Arnesh-sharma/P4P_Project-130/Testing Data/For Report/FETs/FET_CH1_Bodes/WFM02.CSV

in Sa | Frequency in Hz | Gain in dB | Phase in ° | Amplitude in Vpp
1.00E+00 | 1.000E+01 | -6.047E+01 | 1.642E+02 | 2.500E+00
2.00E+00 | 1.047E+01 | -6.065E+01 | 1.676E+02 | 2.500E+00
3.00E+00 | 1.096E+01 | -5.911E+01 | 1.651E+02 | 2.500E+00
4.00E+00 | 1.148E+01 | -5.924E+01 | 1.657E+02 | 2.500E+00
5.00E+00 | 1.202E+01 | -5.991E+01 | 1.629E+02 | 2.500E+00
6.00E+00 | 1.259E+01 | -6.114E+01 | 1.509E+02 | 2.500E+00
7.00E+00 | 1.318E+01 | -6.121E+01 | 1.619E+02 | 2.500E+00
8.00E+00 | 1.380E+01 | -6.082E+01 | 1.474E+02 | 2.500E+00
9.00E+00 | 1.445E+01 | -5.925E+01 | 1.609E+02 | 2.500E+00
1.00E+01 | 1.514E+01 | -6.002E+01 | 1.505E+02 | 2.500E+00
1.10E+01 | 1.585E+01 | -6.094E+01 | 1.486E+02 | 2.500E+00
1.20E+01 | 1.660E+01 | -5.973E+01 | 1.522E+02 | 2.500E+00
1.30E+01 | 1.738E+01 | -5.926E+01 | 1.521E+02 | 2.500E+00
1.40E+01 | 1.820E+01 | -5.986E+01 | 1.493E+02 | 2.500E+00
1.50E+01 | 1.905E+01 | -6.031E+01 | 1.430E+02 | 2.500E+00
1.60E+01 | 1.995E+01 | -6.091E+01 | 1.400E+02 | 2.500E+00
1.70E+01 | 2.089E+01 | -5.957E+01 | 1.442E+02 | 2.500E+00
1.80E+01 | 2.188E+01 | -5.907E+01 | 1.436E+02 | 2.500E+00
1.90E+01 | 2.291E+01 | -5.991E+01 | 1.474E+02 | 2.500E+00
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
