Arnesh-sharma/P4P_Project-130/Testing Data/For Report/FETs/FET_CH2_Bodes/WFM04.CSV

in Sa | Frequency in Hz | Gain in dB | Phase in ° | Amplitude in Vpp
1.00E+00 | 1.000E+01 | -6.008E+01 | 1.688E+02 | 2.500E+00
2.00E+00 | 1.047E+01 | -6.032E+01 | 1.612E+02 | 2.500E+00
3.00E+00 | 1.096E+01 | -5.910E+01 | 1.686E+02 | 2.500E+00
4.00E+00 | 1.148E+01 | -6.008E+01 | 1.629E+02 | 2.500E+00
5.00E+00 | 1.202E+01 | -5.858E+01 | 1.622E+02 | 2.500E+00
6.00E+00 | 1.259E+01 | -5.917E+01 | 1.635E+02 | 2.500E+00
7.00E+00 | 1.318E+01 | -5.980E+01 | 1.564E+02 | 2.500E+00
8.00E+00 | 1.380E+01 | -5.957E+01 | 1.568E+02 | 2.500E+00
9.00E+00 | 1.445E+01 | -6.005E+01 | 1.624E+02 | 2.500E+00
1.00E+01 | 1.514E+01 | -6.035E+01 | 1.547E+02 | 2.500E+00
1.10E+01 | 1.585E+01 | -5.988E+01 | 1.471E+02 | 2.500E+00
1.20E+01 | 1.660E+01 | -6.016E+01 | 1.517E+02 | 2.500E+00
1.30E+01 | 1.738E+01 | -5.981E+01 | 1.529E+02 | 2.500E+00
1.40E+01 | 1.820E+01 | -5.945E+01 | 1.495E+02 | 2.500E+00
1.50E+01 | 1.905E+01 | -6.048E+01 | 1.459E+02 | 2.500E+00
1.60E+01 | 1.995E+01 | -6.108E+01 | 1.517E+02 | 2.500E+00
1.70E+01 | 2.089E+01 | -5.919E+01 | 1.538E+02 | 2.500E+00
1.80E+01 | 2.188E+01 | -6.028E+01 | 1.495E+02 | 2.500E+00
1.90E+01 | 2.291E+01 | -5.945E+01 | 1.537E+02 | 2.500E+00
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
