Arnesh-sharma/P4P_Project-130/Testing Data/For Report/FETs/FET_PCB_CH1_Bodes/WFM05.CSV

in Sa | Frequency in Hz | Gain in dB | Phase in ° | Amplitude in Vpp
1.00E+00 | 1.000E+01 | -3.042E+01 | -7.533E+01 | 2.500E+00
2.00E+00 | 1.047E+01 | -3.042E+01 | -7.579E+01 | 2.500E+00
3.00E+00 | 1.096E+01 | -3.021E+01 | -7.619E+01 | 2.500E+00
4.00E+00 | 1.148E+01 | -3.033E+01 | -7.878E+01 | 2.500E+00
5.00E+00 | 1.202E+01 | -3.009E+01 | -7.882E+01 | 2.500E+00
6.00E+00 | 1.259E+01 | -3.027E+01 | -8.114E+01 | 2.500E+00
7.00E+00 | 1.318E+01 | -3.026E+01 | -8.289E+01 | 2.500E+00
8.00E+00 | 1.380E+01 | -3.015E+01 | -8.408E+01 | 2.500E+00
9.00E+00 | 1.445E+01 | -3.002E+01 | -8.246E+01 | 2.500E+00
1.00E+01 | 1.514E+01 | -3.021E+01 | -8.605E+01 | 2.500E+00
1.10E+01 | 1.585E+01 | -3.003E+01 | -8.678E+01 | 2.500E+00
1.20E+01 | 1.660E+01 | -2.995E+01 | -8.854E+01 | 2.500E+00
1.30E+01 | 1.738E+01 | -2.990E+01 | -8.868E+01 | 2.500E+00
1.40E+01 | 1.820E+01 | -3.001E+01 | -9.140E+01 | 2.500E+00
1.50E+01 | 1.905E+01 | -3.006E+01 | -9.274E+01 | 2.500E+00
1.60E+01 | 1.995E+01 | -2.995E+01 | -9.309E+01 | 2.500E+00
1.70E+01 | 2.089E+01 | -2.965E+01 | -9.219E+01 | 2.500E+00
1.80E+01 | 2.188E+01 | -2.967E+01 | -9.439E+01 | 2.500E+00
1.90E+01 | 2.291E+01 | -2.963E+01 | -9.443E+01 | 2.500E+00
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
