Arnesh-sharma/P4P_Project-130/Testing Data/For Report/FETs/FET_PCB_CH2_Bodes/WFM07.CSV

in Sa | Frequency in Hz | Gain in dB | Phase in ° | Amplitude in Vpp
1.00E+00 | 1.000E+01 | -6.133E+01 | 1.636E+02 | 2.500E+00
2.00E+00 | 1.047E+01 | -6.054E+01 | 1.682E+02 | 2.500E+00
3.00E+00 | 1.096E+01 | -6.137E+01 | 1.630E+02 | 2.500E+00
4.00E+00 | 1.148E+01 | -6.084E+01 | 1.671E+02 | 2.500E+00
5.00E+00 | 1.202E+01 | -5.939E+01 | 1.590E+02 | 2.500E+00
6.00E+00 | 1.259E+01 | -6.143E+01 | 1.571E+02 | 2.500E+00
7.00E+00 | 1.318E+01 | -6.131E+01 | 1.496E+02 | 2.500E+00
8.00E+00 | 1.380E+01 | -6.033E+01 | 1.673E+02 | 2.500E+00
9.00E+00 | 1.445E+01 | -5.975E+01 | 1.576E+02 | 2.500E+00
1.00E+01 | 1.514E+01 | -6.128E+01 | 1.471E+02 | 2.500E+00
1.10E+01 | 1.585E+01 | -6.025E+01 | 1.496E+02 | 2.500E+00
1.20E+01 | 1.660E+01 | -6.090E+01 | 1.441E+02 | 2.500E+00
1.30E+01 | 1.738E+01 | -6.105E+01 | 1.563E+02 | 2.500E+00
1.40E+01 | 1.820E+01 | -6.109E+01 | 1.546E+02 | 2.500E+00
1.50E+01 | 1.905E+01 | -6.118E+01 | 1.469E+02 | 2.500E+00
1.60E+01 | 1.995E+01 | -6.015E+01 | 1.507E+02 | 2.500E+00
1.70E+01 | 2.089E+01 | -6.005E+01 | 1.497E+02 | 2.500E+00
1.80E+01 | 2.188E+01 | -6.015E+01 | 1.510E+02 | 2.500E+00
1.90E+01 | 2.291E+01 | -5.955E+01 | 1.421E+02 | 2.500E+00
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
