Arnesh-sharma/P4P_Project-130/Testing Data/For Report/FETs/self-biasing/WFM06.CSV

in Sa | Frequency in Hz | Gain in dB | Phase in ° | Amplitude in Vpp
1.00E+00 | 1.000E+01 | -6.061E+01 | 1.585E+02 | 2.500E+00
2.00E+00 | 1.047E+01 | -6.017E+01 | 1.648E+02 | 2.500E+00
3.00E+00 | 1.096E+01 | -5.976E+01 | 1.714E+02 | 2.500E+00
4.00E+00 | 1.148E+01 | -5.970E+01 | 1.749E+02 | 2.500E+00
5.00E+00 | 1.202E+01 | -6.005E+01 | 1.654E+02 | 2.500E+00
6.00E+00 | 1.259E+01 | -6.053E+01 | 1.615E+02 | 2.500E+00
7.00E+00 | 1.318E+01 | -6.161E+01 | 1.511E+02 | 2.500E+00
8.00E+00 | 1.380E+01 | -6.113E+01 | 1.616E+02 | 2.500E+00
9.00E+00 | 1.445E+01 | -6.097E+01 | 1.599E+02 | 2.500E+00
1.00E+01 | 1.514E+01 | -6.154E+01 | 1.647E+02 | 2.500E+00
1.10E+01 | 1.585E+01 | -6.083E+01 | 1.540E+02 | 2.500E+00
1.20E+01 | 1.660E+01 | -6.118E+01 | 1.557E+02 | 2.500E+00
1.30E+01 | 1.738E+01 | -6.055E+01 | 1.540E+02 | 2.500E+00
1.40E+01 | 1.820E+01 | -6.116E+01 | 1.457E+02 | 2.500E+00
1.50E+01 | 1.905E+01 | -6.225E+01 | 1.432E+02 | 2.500E+00
1.60E+01 | 1.995E+01 | -6.075E+01 | 1.471E+02 | 2.500E+00
1.70E+01 | 2.089E+01 | -6.008E+01 | 1.429E+02 | 2.500E+00
1.80E+01 | 2.188E+01 | -5.997E+01 | 1.408E+02 | 2.500E+00
1.90E+01 | 2.291E+01 | -6.139E+01 | 1.360E+02 | 2.500E+00
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
