Arnesh-sharma/P4P_Project-130/Testing Data/For Report/FETs/self-biasing/WFM08.CSV

in Sa | Frequency in Hz | Gain in dB | Phase in ° | Amplitude in Vpp
1.00E+00 | 1.000E+01 | -6.133E+01 | 1.578E+02 | 2.500E+00
2.00E+00 | 1.047E+01 | -6.377E+01 | 1.590E+02 | 2.500E+00
3.00E+00 | 1.096E+01 | -6.002E+01 | 1.534E+02 | 2.500E+00
4.00E+00 | 1.148E+01 | -6.130E+01 | 1.545E+02 | 2.500E+00
5.00E+00 | 1.202E+01 | -6.123E+01 | 1.655E+02 | 2.500E+00
6.00E+00 | 1.259E+01 | -6.051E+01 | 1.588E+02 | 2.500E+00
7.00E+00 | 1.318E+01 | -6.065E+01 | 1.642E+02 | 2.500E+00
8.00E+00 | 1.380E+01 | -6.114E+01 | 1.550E+02 | 2.500E+00
9.00E+00 | 1.445E+01 | -5.991E+01 | 1.567E+02 | 2.500E+00
1.00E+01 | 1.514E+01 | -6.283E+01 | 1.500E+02 | 2.500E+00
1.10E+01 | 1.585E+01 | -6.063E+01 | 1.496E+02 | 2.500E+00
1.20E+01 | 1.660E+01 | -6.056E+01 | 1.499E+02 | 2.500E+00
1.30E+01 | 1.738E+01 | -5.967E+01 | 1.531E+02 | 2.500E+00
1.40E+01 | 1.820E+01 | -6.410E+01 | 1.441E+02 | 2.500E+00
1.50E+01 | 1.905E+01 | -6.209E+01 | 1.359E+02 | 2.500E+00
1.60E+01 | 1.995E+01 | -6.193E+01 | 1.447E+02 | 2.500E+00
1.70E+01 | 2.089E+01 | -5.917E+01 | 1.486E+02 | 2.500E+00
1.80E+01 | 2.188E+01 | -6.021E+01 | 1.463E+02 | 2.500E+00
1.90E+01 | 2.291E+01 | -6.020E+01 | 1.390E+02 | 2.500E+00
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
