Arnesh-sharma/P4P_Project-130/Testing Data/For Report/Instrumentation Amp Circuit/Capacitors Shorted/WFM08.CSV

in Sa | Frequency in Hz | Gain in dB | Phase in ° | Amplitude in Vpp
1.00E+00 | 1.000E+01 | -5.101E+01 | 9.313E+01 | 2.500E+00
2.00E+00 | 1.047E+01 | -5.222E+01 | 7.926E+01 | 2.500E+00
3.00E+00 | 1.096E+01 | -5.104E+01 | 8.657E+01 | 2.500E+00
4.00E+00 | 1.148E+01 | -4.765E+01 | 7.619E+01 | 2.500E+00
5.00E+00 | 1.202E+01 | -4.724E+01 | 1.038E+02 | 2.500E+00
6.00E+00 | 1.259E+01 | -4.641E+01 | 9.072E+01 | 2.500E+00
7.00E+00 | 1.318E+01 | -4.665E+01 | 9.873E+01 | 2.500E+00
8.00E+00 | 1.380E+01 | -4.859E+01 | 8.802E+01 | 2.500E+00
9.00E+00 | 1.445E+01 | -5.057E+01 | 9.474E+01 | 2.500E+00
1.00E+01 | 1.514E+01 | -4.840E+01 | 8.466E+01 | 2.500E+00
1.10E+01 | 1.585E+01 | -4.513E+01 | 7.512E+01 | 2.500E+00
1.20E+01 | 1.660E+01 | -4.788E+01 | 8.815E+01 | 2.500E+00
1.30E+01 | 1.738E+01 | -4.551E+01 | 7.494E+01 | 2.500E+00
1.40E+01 | 1.820E+01 | -4.634E+01 | 9.491E+01 | 2.500E+00
1.50E+01 | 1.905E+01 | -4.476E+01 | 7.654E+01 | 2.500E+00
1.60E+01 | 1.995E+01 | -4.693E+01 | 7.954E+01 | 2.500E+00
1.70E+01 | 2.089E+01 | -4.634E+01 | 9.863E+01 | 2.500E+00
1.80E+01 | 2.188E+01 | -4.537E+01 | 8.156E+01 | 2.500E+00
1.90E+01 | 2.291E+01 | -4.388E+01 | 9.160E+01 | 2.500E+00
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
