Arnesh-sharma/P4P_Project-130/Testing Data/For Report/archieved/Larger_distance/WFM02.CSV

in Sa | Frequency in Hz | Gain in dB | Phase in ° | Amplitude in Vpp
1.00E+00 | 1.000E+01 | -5.203E+01 | 1.149E+02 | 2.500E+00
2.00E+00 | 1.047E+01 | -5.043E+01 | 1.090E+02 | 2.500E+00
3.00E+00 | 1.096E+01 | -5.006E+01 | 1.136E+02 | 2.500E+00
4.00E+00 | 1.148E+01 | -4.958E+01 | 1.174E+02 | 2.500E+00
5.00E+00 | 1.202E+01 | -4.828E+01 | 1.049E+02 | 2.500E+00
6.00E+00 | 1.259E+01 | -4.667E+01 | 1.065E+02 | 2.500E+00
7.00E+00 | 1.318E+01 | -4.695E+01 | 8.723E+01 | 2.500E+00
8.00E+00 | 1.380E+01 | -4.717E+01 | 1.143E+02 | 2.500E+00
9.00E+00 | 1.445E+01 | -4.784E+01 | 1.038E+02 | 2.500E+00
1.00E+01 | 1.514E+01 | -4.713E+01 | 1.044E+02 | 2.500E+00
1.10E+01 | 1.585E+01 | -4.480E+01 | 1.026E+02 | 2.500E+00
1.20E+01 | 1.660E+01 | -4.749E+01 | 1.006E+02 | 2.500E+00
1.30E+01 | 1.738E+01 | -4.628E+01 | 1.056E+02 | 2.500E+00
1.40E+01 | 1.820E+01 | -4.692E+01 | 9.501E+01 | 2.500E+00
1.50E+01 | 1.905E+01 | -4.497E+01 | 1.049E+02 | 2.500E+00
1.60E+01 | 1.995E+01 | -4.505E+01 | 8.538E+01 | 2.500E+00
1.70E+01 | 2.089E+01 | -4.315E+01 | 8.804E+01 | 2.500E+00
1.80E+01 | 2.188E+01 | -4.538E+01 | 8.958E+01 | 2.500E+00
1.90E+01 | 2.291E+01 | -4.209E+01 | 9.914E+01 | 2.500E+00
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
