Arnesh-sharma/P4P_Project-130/Testing Data/For Report/FETs/single_stage/WFM01.CSV

in Sa | Frequency in Hz | Gain in dB | Phase in ° | Amplitude in Vpp
1.00E+00 | 1.000E+01 | -5.988E+01 | 1.644E+02 | 2.500E+00
2.00E+00 | 1.047E+01 | -6.120E+01 | 1.702E+02 | 2.500E+00
3.00E+00 | 1.096E+01 | -5.895E+01 | 1.637E+02 | 2.500E+00
4.00E+00 | 1.148E+01 | -5.893E+01 | 1.624E+02 | 2.500E+00
5.00E+00 | 1.202E+01 | -5.933E+01 | 1.627E+02 | 2.500E+00
6.00E+00 | 1.259E+01 | -5.953E+01 | 1.594E+02 | 2.500E+00
7.00E+00 | 1.318E+01 | -6.090E+01 | 1.557E+02 | 2.500E+00
8.00E+00 | 1.380E+01 | -6.072E+01 | 1.570E+02 | 2.500E+00
9.00E+00 | 1.445E+01 | -5.999E+01 | 1.594E+02 | 2.500E+00
1.00E+01 | 1.514E+01 | -6.031E+01 | 1.593E+02 | 2.500E+00
1.10E+01 | 1.585E+01 | -6.077E+01 | 1.564E+02 | 2.500E+00
1.20E+01 | 1.660E+01 | -6.075E+01 | 1.445E+02 | 2.500E+00
1.30E+01 | 1.738E+01 | -6.028E+01 | 1.560E+02 | 2.500E+00
1.40E+01 | 1.820E+01 | -6.079E+01 | 1.498E+02 | 2.500E+00
1.50E+01 | 1.905E+01 | -6.085E+01 | 1.419E+02 | 2.500E+00
1.60E+01 | 1.995E+01 | -5.956E+01 | 1.446E+02 | 2.500E+00
1.70E+01 | 2.089E+01 | -5.898E+01 | 1.546E+02 | 2.500E+00
1.80E+01 | 2.188E+01 | -5.962E+01 | 1.493E+02 | 2.500E+00
1.90E+01 | 2.291E+01 | -5.903E+01 | 1.380E+02 | 2.500E+00
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
