Arnesh-sharma/P4P_Project-130/Testing Data/For Report/FETs/single_stage/WFM03.CSV

in Sa | Frequency in Hz | Gain in dB | Phase in ° | Amplitude in Vpp
1.00E+00 | 1.000E+01 | -5.998E+01 | 1.650E+02 | 2.500E+00
2.00E+00 | 1.047E+01 | -6.008E+01 | 1.716E+02 | 2.500E+00
3.00E+00 | 1.096E+01 | -5.981E+01 | 1.618E+02 | 2.500E+00
4.00E+00 | 1.148E+01 | -6.136E+01 | 1.599E+02 | 2.500E+00
5.00E+00 | 1.202E+01 | -6.048E+01 | 1.658E+02 | 2.500E+00
6.00E+00 | 1.259E+01 | -6.148E+01 | 1.579E+02 | 2.500E+00
7.00E+00 | 1.318E+01 | -5.994E+01 | 1.582E+02 | 2.500E+00
8.00E+00 | 1.380E+01 | -5.983E+01 | 1.653E+02 | 2.500E+00
9.00E+00 | 1.445E+01 | -5.953E+01 | 1.660E+02 | 2.500E+00
1.00E+01 | 1.514E+01 | -6.018E+01 | 1.623E+02 | 2.500E+00
1.10E+01 | 1.585E+01 | -6.015E+01 | 1.556E+02 | 2.500E+00
1.20E+01 | 1.660E+01 | -5.983E+01 | 1.547E+02 | 2.500E+00
1.30E+01 | 1.738E+01 | -5.961E+01 | 1.544E+02 | 2.500E+00
1.40E+01 | 1.820E+01 | -6.047E+01 | 1.511E+02 | 2.500E+00
1.50E+01 | 1.905E+01 | -6.066E+01 | 1.537E+02 | 2.500E+00
1.60E+01 | 1.995E+01 | -6.006E+01 | 1.462E+02 | 2.500E+00
1.70E+01 | 2.089E+01 | -5.886E+01 | 1.445E+02 | 2.500E+00
1.80E+01 | 2.188E+01 | -5.851E+01 | 1.504E+02 | 2.500E+00
1.90E+01 | 2.291E+01 | -6.026E+01 | 1.458E+02 | 2.500E+00
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
