Arnesh-sharma/P4P_Project-130/Matlab Code/Electret_sensor/300Hz_electret.png

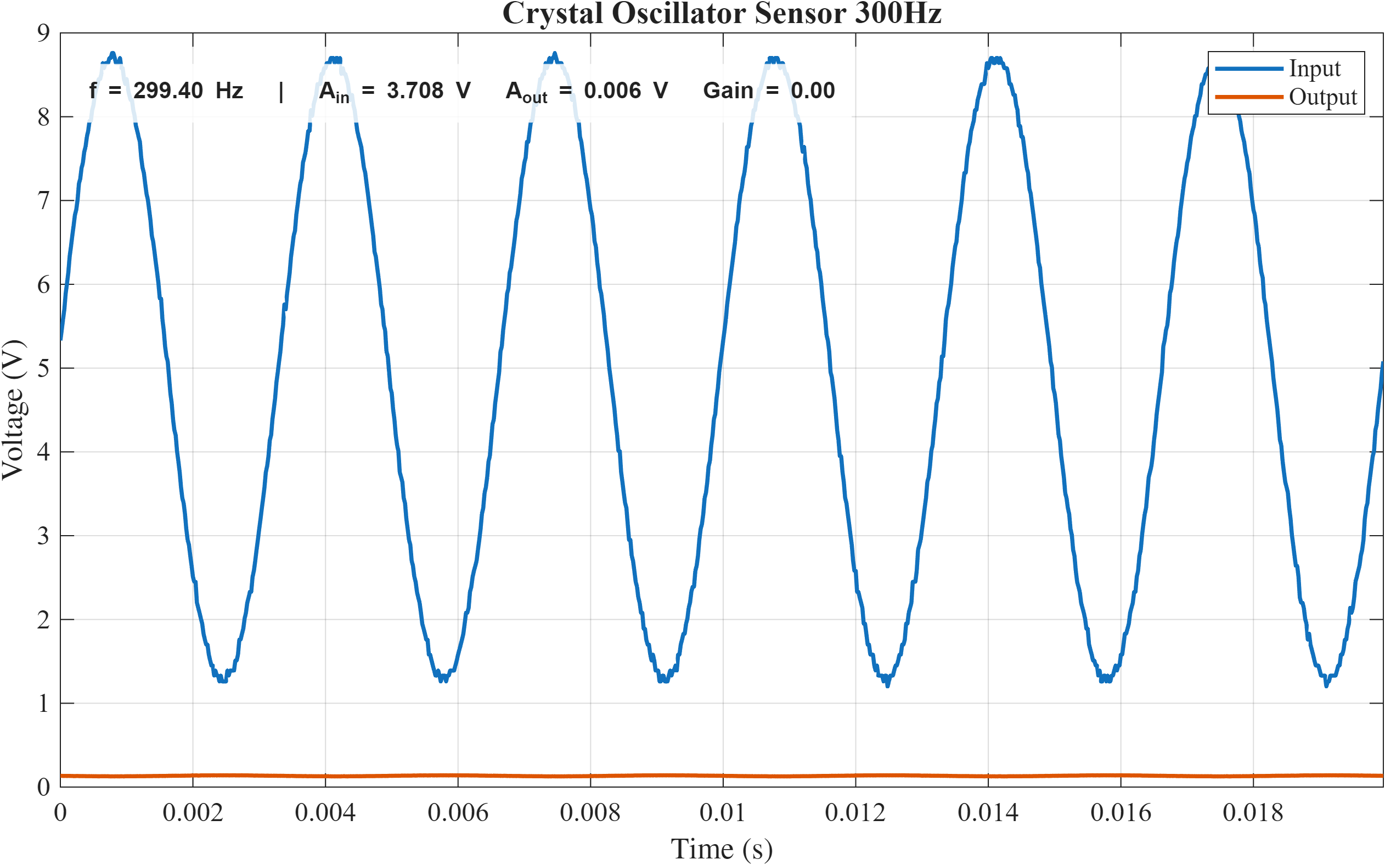
Matlab Code/Electret_sensor/300Hz_electret.png
