Arnesh-sharma/P4P_Project-130/Matlab Code/Electret_sensor/electret_plot.png

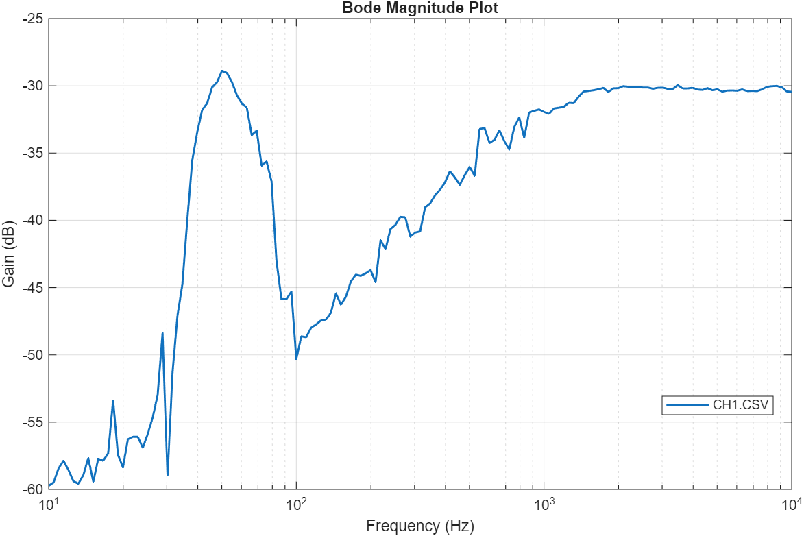
Matlab Code/Electret_sensor/electret_plot.png
