Arnesh-sharma/P4P_Project-130/Matlab Code/electret_single_labelled.png

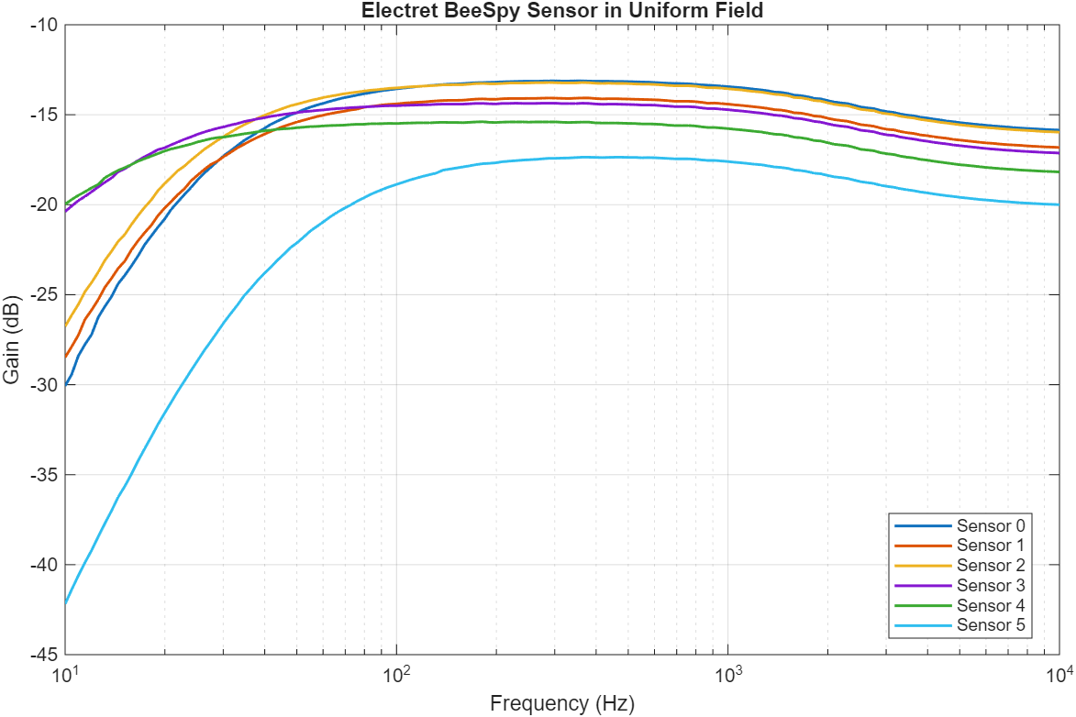
Matlab Code/electret_single_labelled.png
