Arnesh-sharma/P4P_Project-130/Matlab Code/IA_Sensor_Data/combined_bode_(inc short channel).png

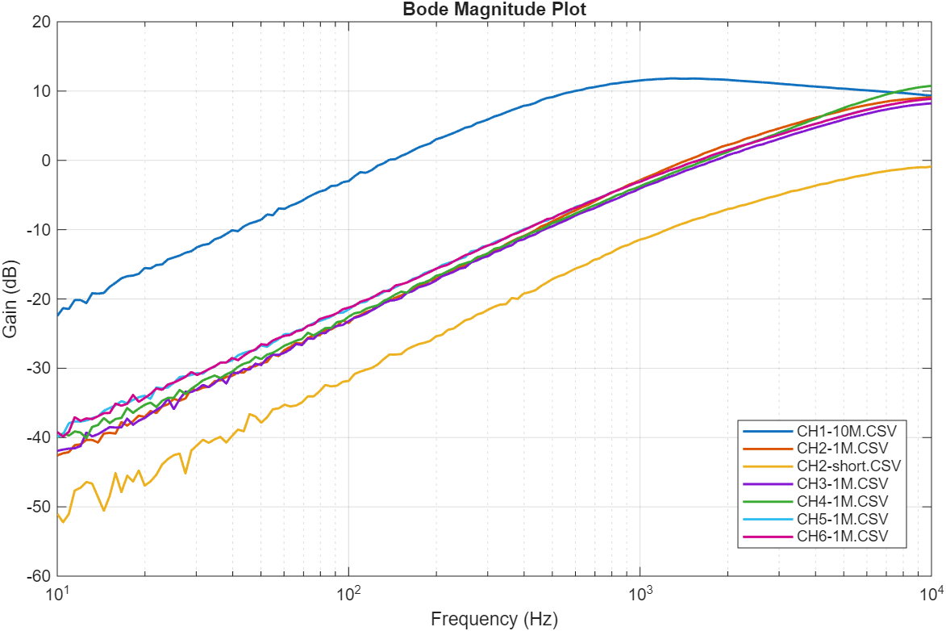
Matlab Code/IA_Sensor_Data/combined_bode_(inc short channel).png
