Arnesh-sharma/P4P_Project-130/Matlab Code/IA_Sensor_Data/instrumentation_amp_plot.png

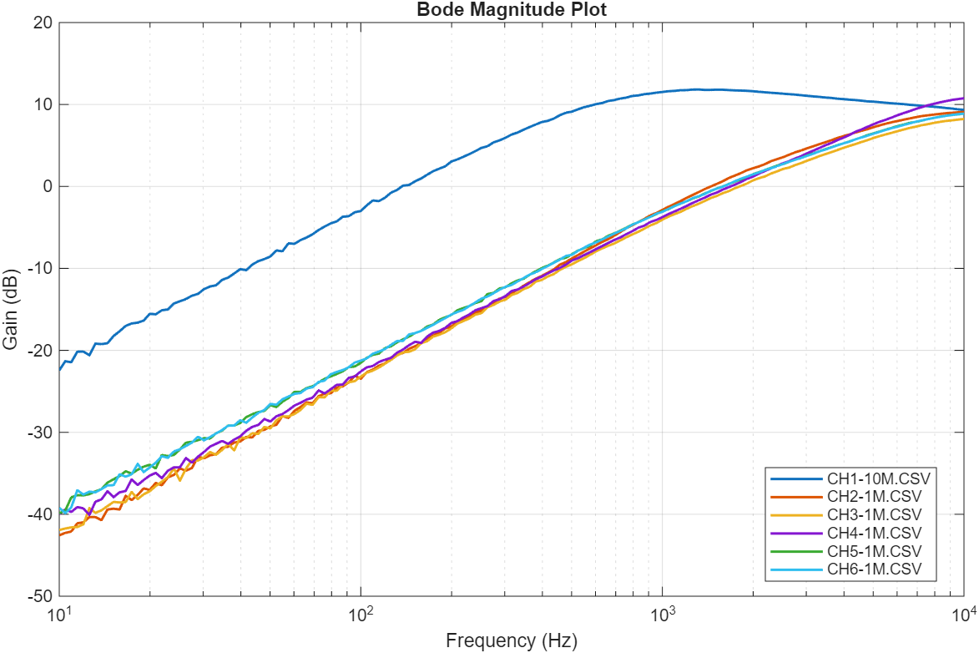
Matlab Code/IA_Sensor_Data/instrumentation_amp_plot.png
