Arnesh-sharma/P4P_Project-130/Matlab Code/jfet_plate_labelled.png

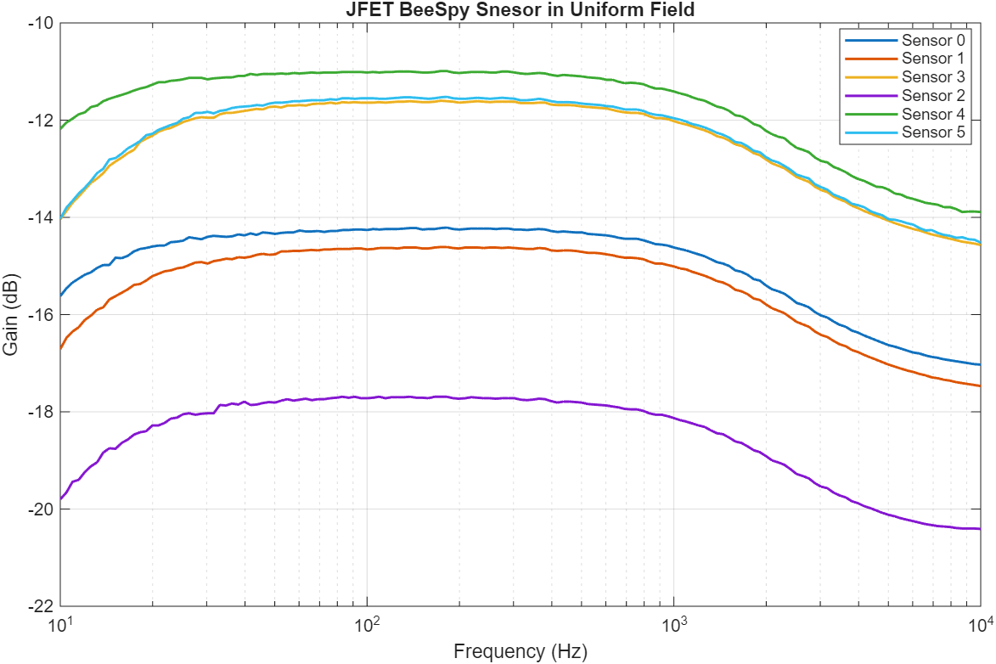
Matlab Code/jfet_plate_labelled.png
