Arnesh-sharma/P4P_Project-130/Matlab Code/jfet_vero_self_biasing.png

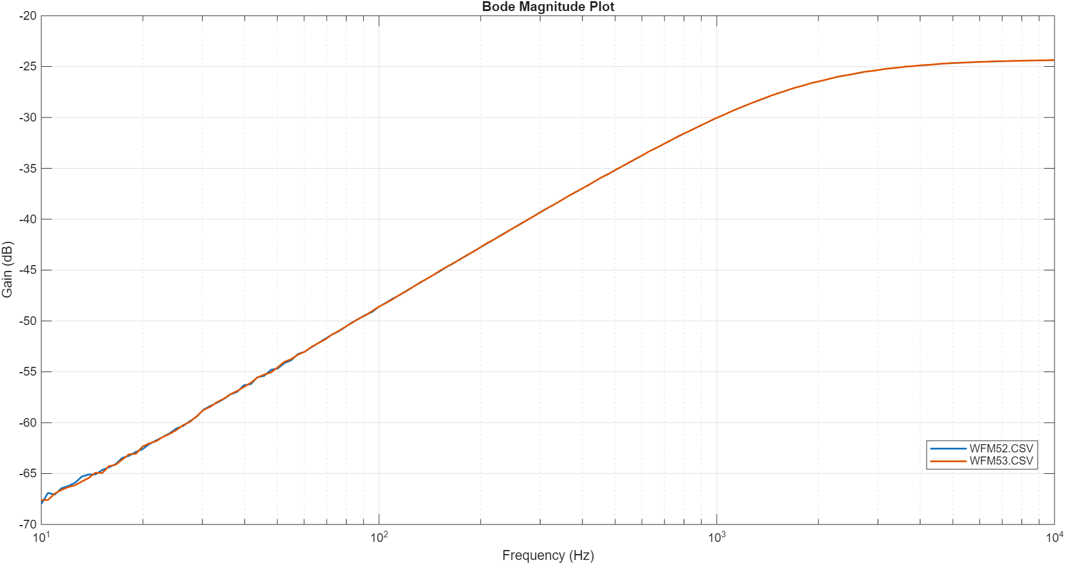
Matlab Code/jfet_vero_self_biasing.png
