Arnesh-sharma/P4P_Project-130/Matlab Code/jfet_vero_single_stage_CH2.png

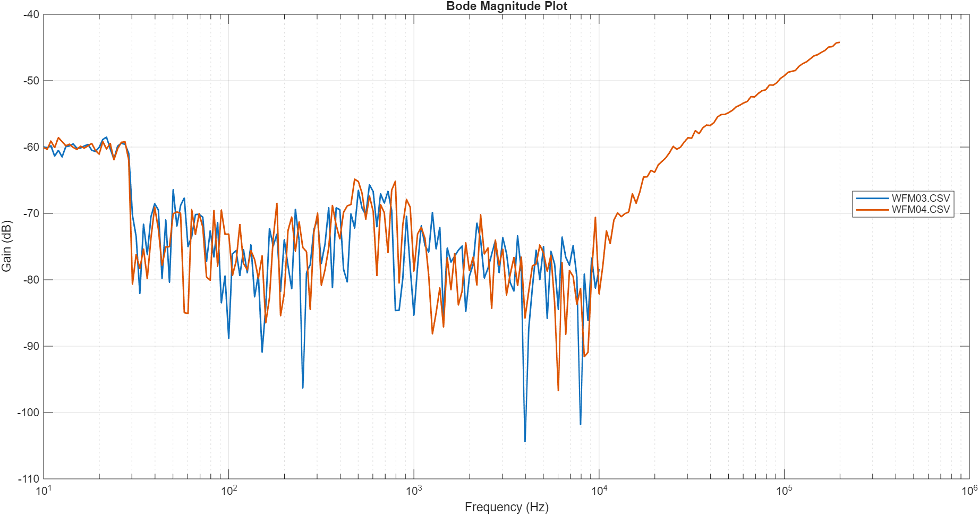
Matlab Code/jfet_vero_single_stage_CH2.png
