Arnesh-sharma/P4P_Project-130/Photos/10Meg Resistor Chain.jpg

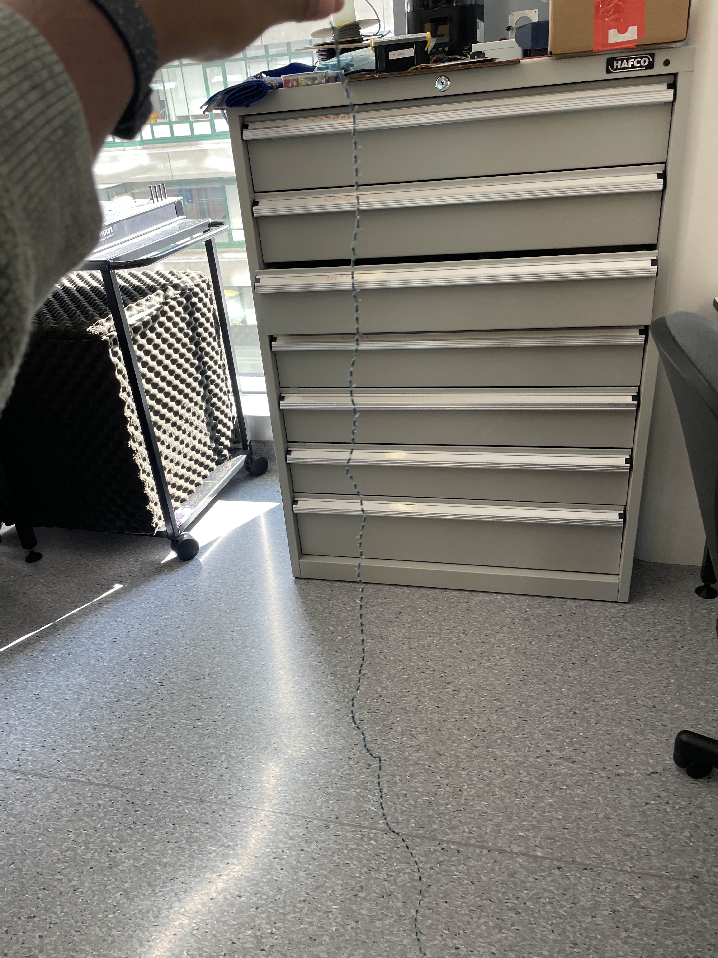
Photos/10Meg Resistor Chain.jpg
