Arnesh-sharma/P4P_Project-130/Photos/image.png

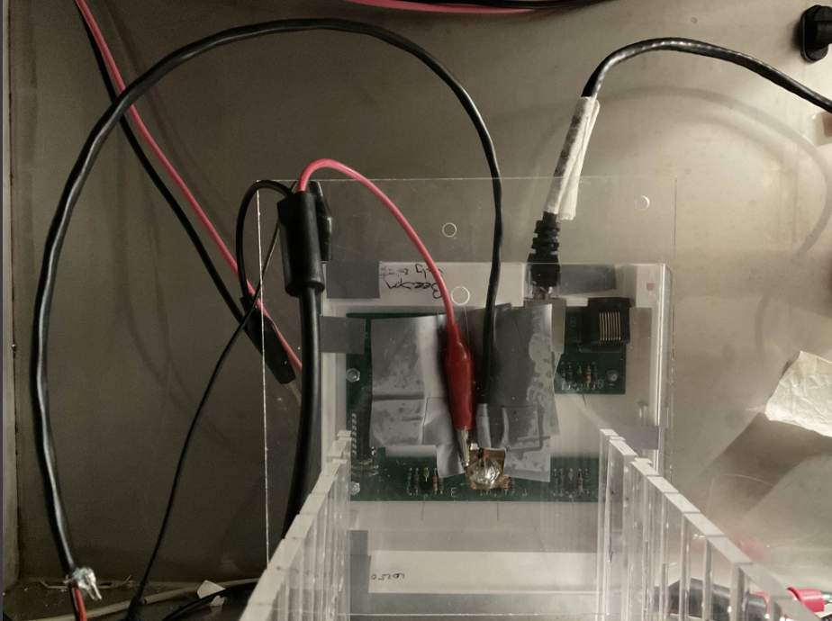
Photos/image.png
