Arnesh-sharma/P4P_Project-130/Photos/IMG_1778.jpg

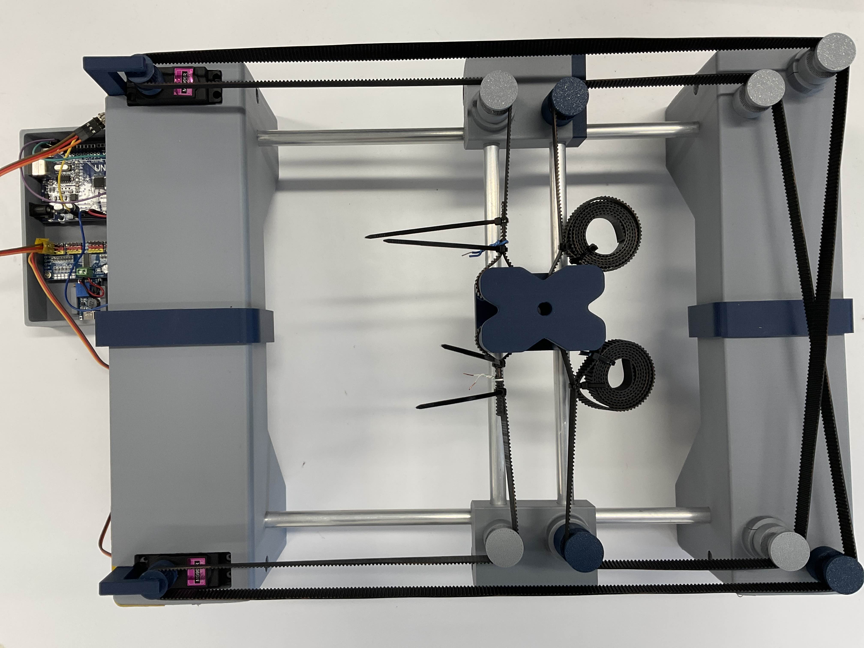
Photos/IMG_1778.jpg
