Arnesh-sharma/P4P_Project-130/Photos/IMG_6400.JPG

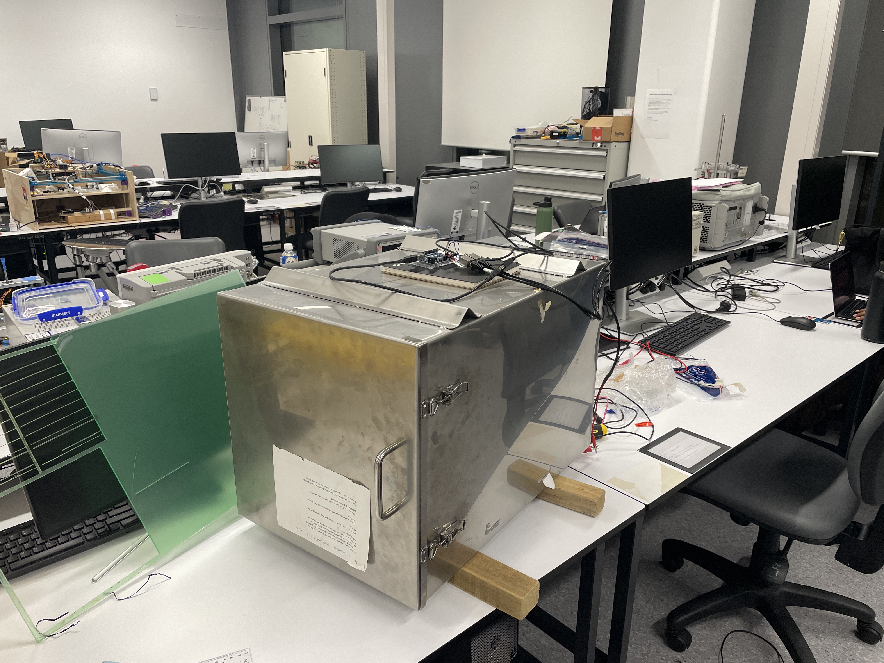
Photos/IMG_6400.JPG
