Arnesh-sharma/P4P_Project-130/Photos/IMG_6402.JPG

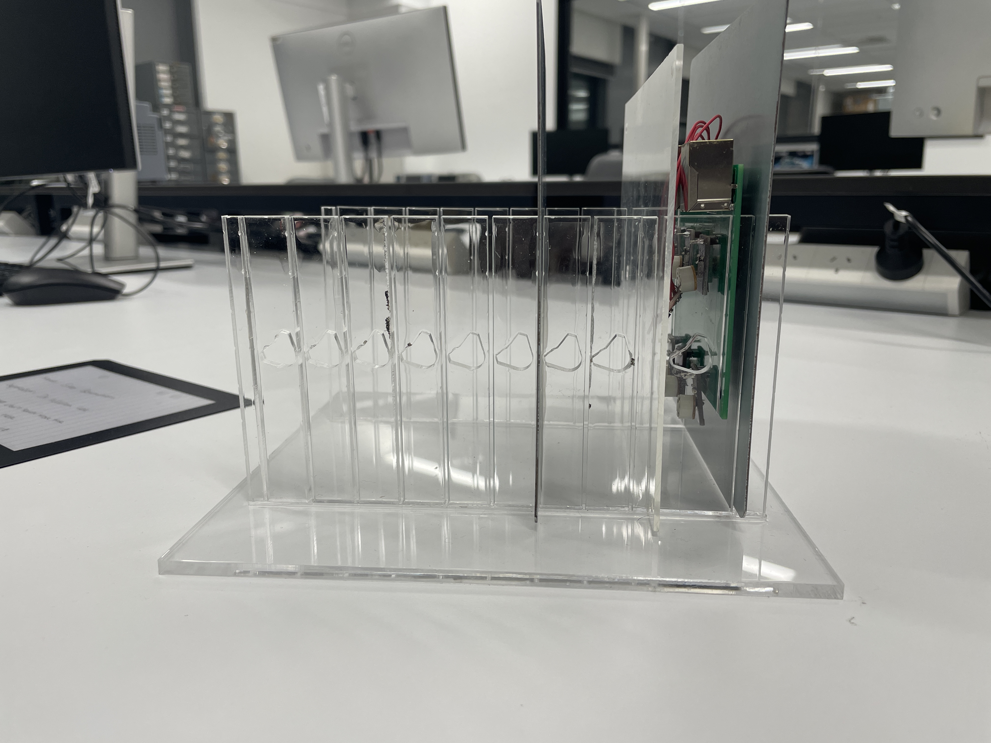
Photos/IMG_6402.JPG
