Arnesh-sharma/P4P_Project-130/Photos/photos of sensors/IMG_6626.jpg

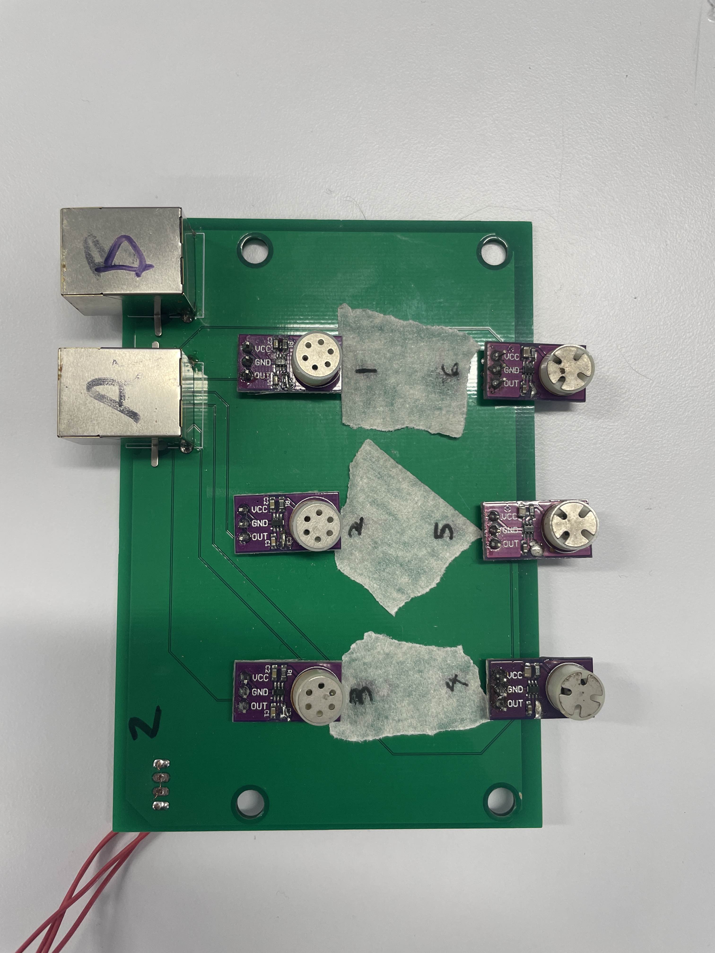
Photos/photos of sensors/IMG_6626.jpg
