Arnesh-sharma/P4P_Project-130/Testing Data/Bee_Hive_Test/Graphs For Report/beetest_6_d3.png

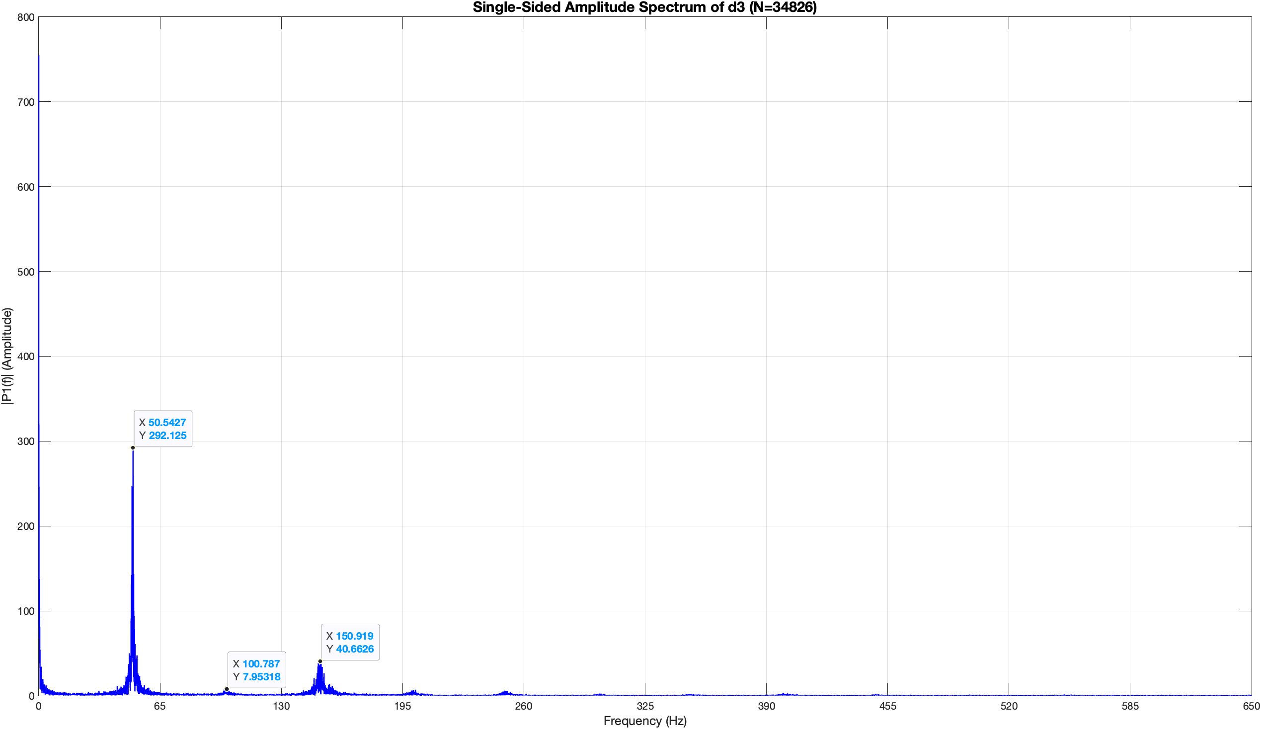
Testing Data/Bee_Hive_Test/Graphs For Report/beetest_6_d3.png
