Arnesh-sharma/P4P_Project-130/Testing Data/For Report/Crystal 16MHz/cry1/cry1_250.png

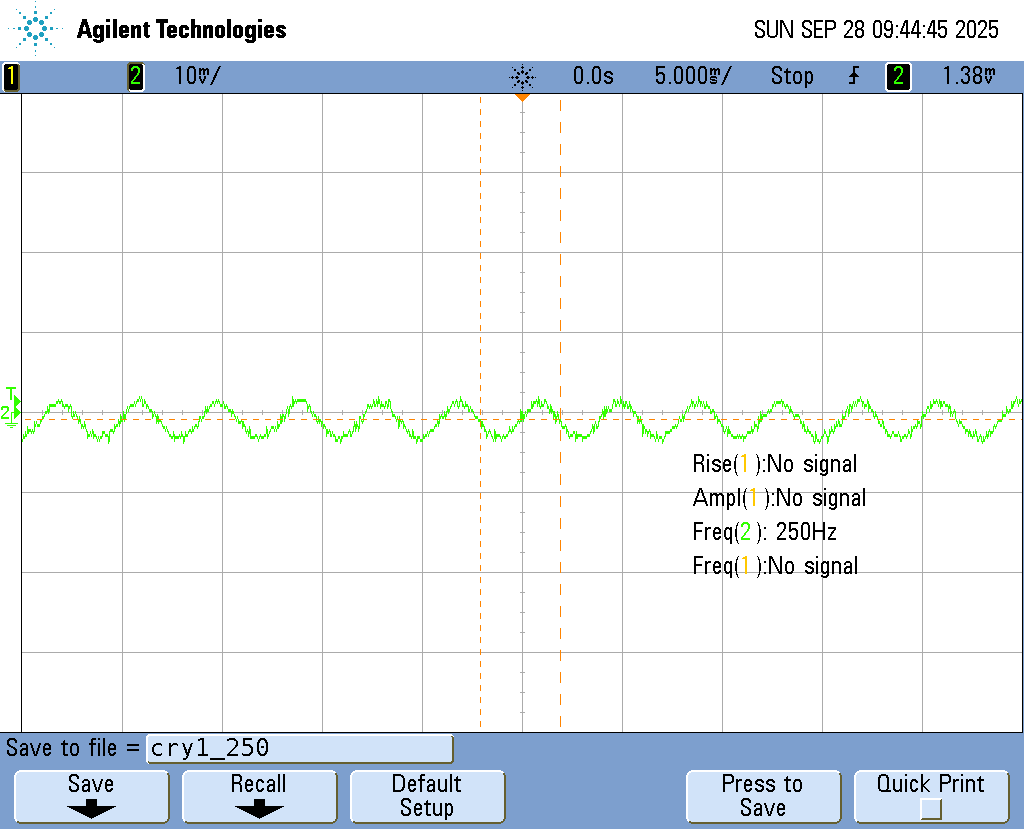
Testing Data/For Report/Crystal 16MHz/cry1/cry1_250.png
