Arnesh-sharma/P4P_Project-130/Testing Data/For Report/Crystal 16MHz/cry2/cry2_15.png

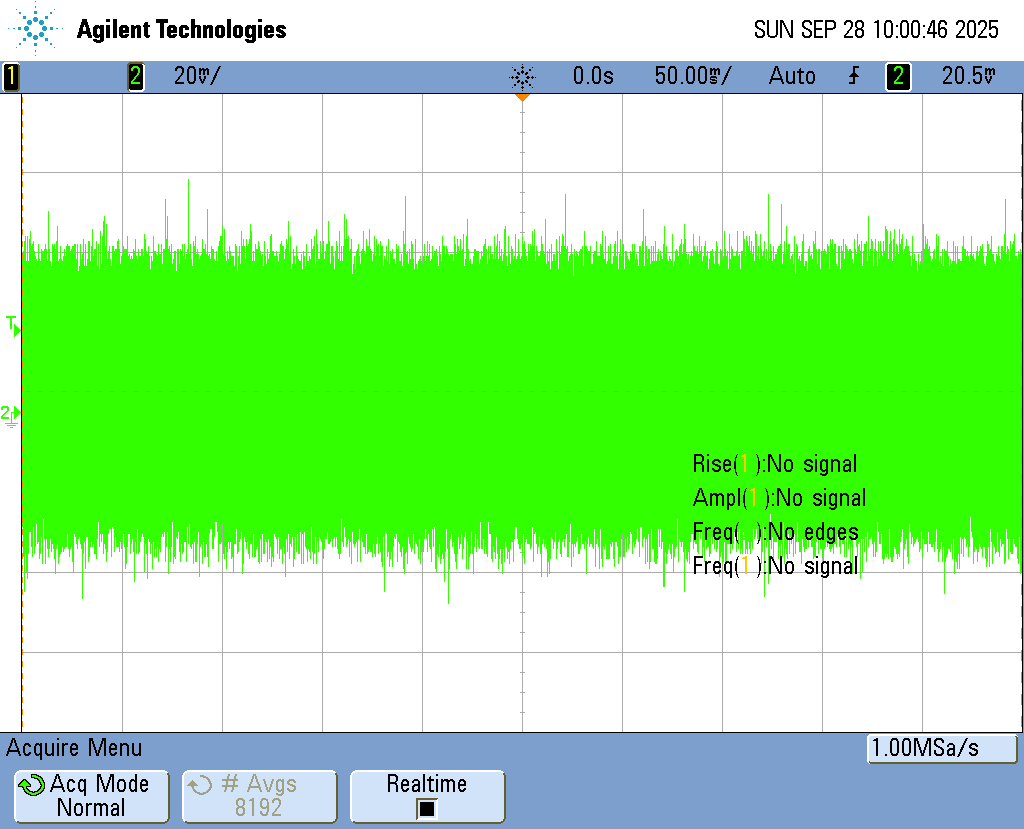
Testing Data/For Report/Crystal 16MHz/cry2/cry2_15.png
