Arnesh-sharma/P4P_Project-130/Testing Data/For Report/Crystal 16MHz/cry3/cry3_25.png

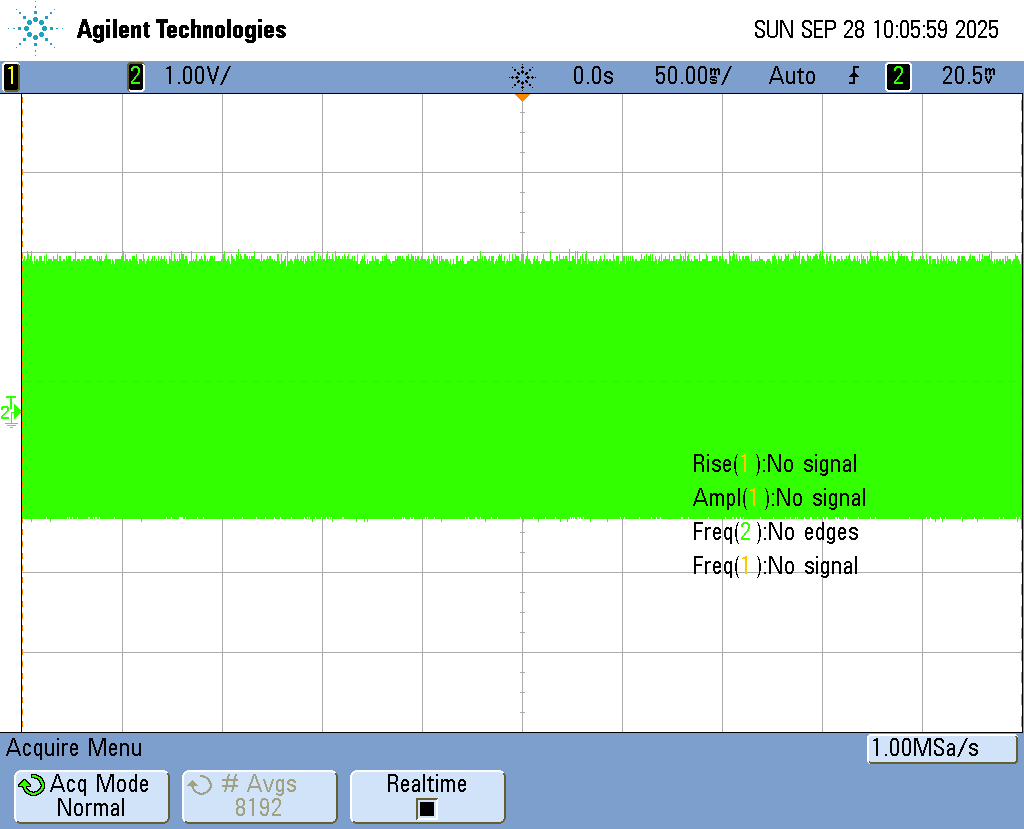
Testing Data/For Report/Crystal 16MHz/cry3/cry3_25.png
