Arnesh-sharma/P4P_Project-130/Testing Data/For Report/Crystal 16MHz/cry4/cry4_150.png

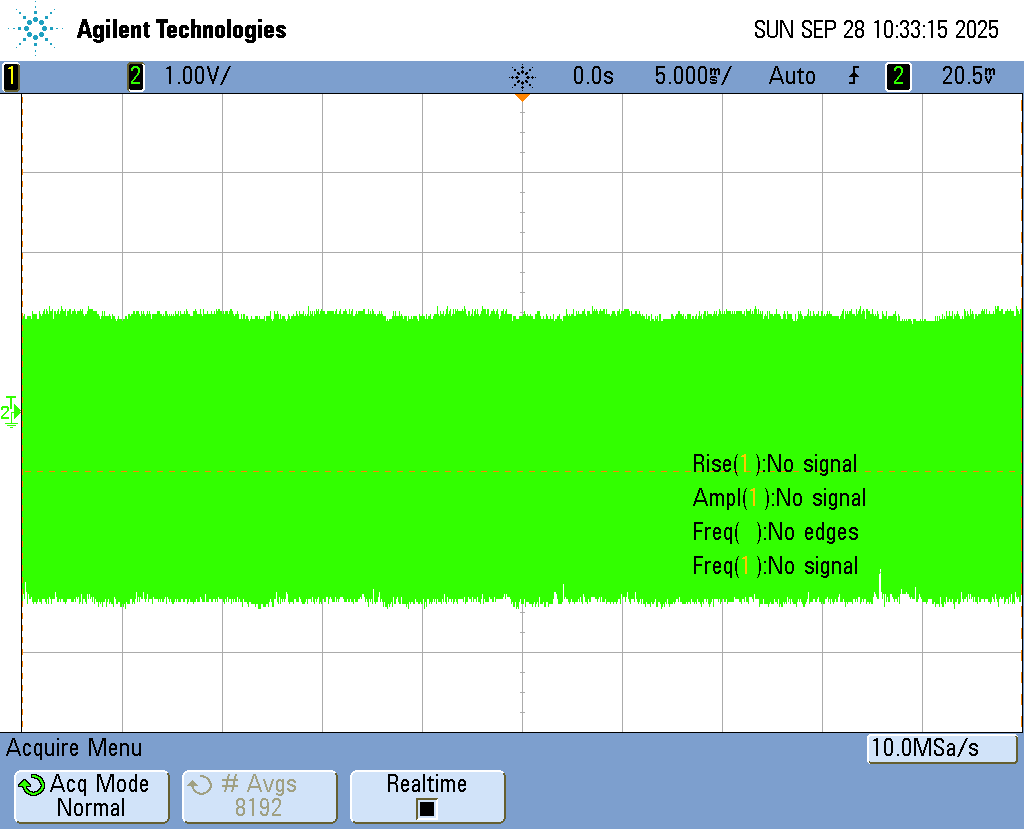
Testing Data/For Report/Crystal 16MHz/cry4/cry4_150.png
