Arnesh-sharma/P4P_Project-130/Testing Data/For Report/Crystal 16MHz/cry5/cry5_100.png

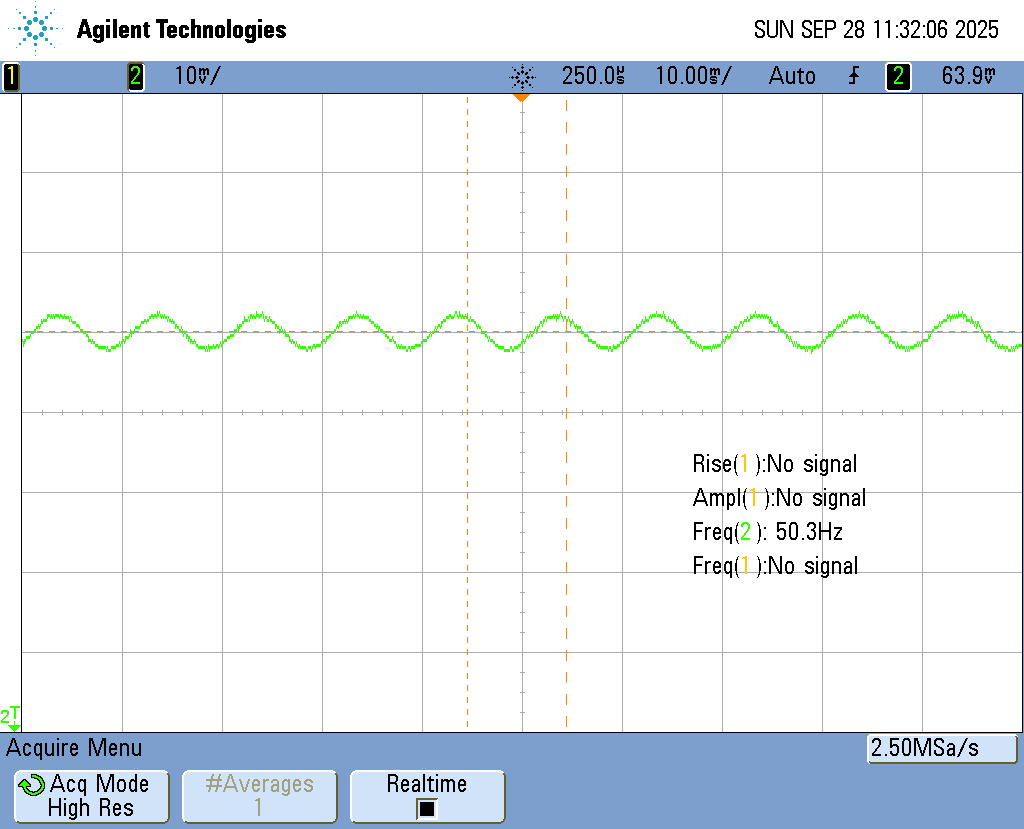
Testing Data/For Report/Crystal 16MHz/cry5/cry5_100.png
