Arnesh-sharma/P4P_Project-130/Testing Data/For Report/FETs/FET_Vero(2).jpg

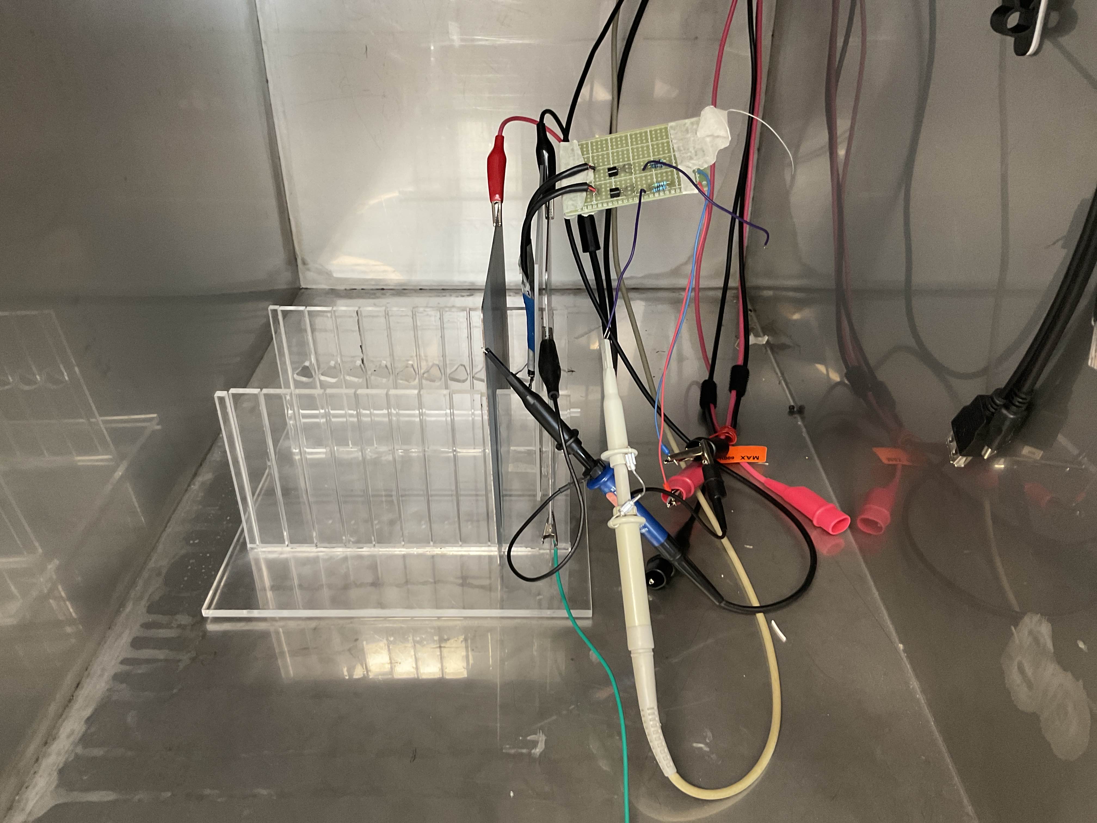
Testing Data/For Report/FETs/FET_Vero(2).jpg
