Arnesh-sharma/P4P_Project-130/PCBs/low_noise_amp/low_noise_amp_IA_opamp/Project Outputs for lna/lna_ia_opamp.xls

Sheet: BOM Report
Bill of Materials |  |  | <Parameter Title not found>
Source Data From: |  | lna_ia_opamp.PrjPcb
Project: |  | lna_ia_opamp.PrjPcb
Variant: |  | None
Creation Date: | 3/7/2016 | 9:22:28 AM
Print Date: | 42436 | 42436.39066
Footprint | Comment | LibRef | Designator | Description | Quantity
DFN10 | LT3042 | LT3042 | *U1 | LowNoise Vreg | 1
ECE-CAPC1608-0603SM | 1nF | CAP000618 | C1, C4 | CAP CER 10nF 50V X7R SM0603 | 2
ECE-CAPC1608-0603SM | 100nF | CAP000624 | C2, C3, C5, C6, C7, C9, C10, C14, C15 | CAP CER 100nF 25V X7R SM0603 | 9
ECE-CAPAE4X5.4SM | 10uF | CAP000303 | C8 | CAP 10uF 16V ELE SM | 1
CAP 1206 | 4.7uF | CAP000530 | C11, C13 | CAP CER 1uF 50V X7R SM0805 | 2
ECE-CAPC2012-0805SM | 1uF | CAP000530 | C12 | CAP CER 1uF 50V X7R SM0805 | 1
ECE-CAPC1608-0603SM | 1000pF | CAP000612 | C16, C17 | CAP CER 1000pF 50V X7R SM0603 | 2
ECE-HDR1TH | Test pin | CON000017 | J1, J2 | TEST PIN | 2
CC2012-0805 | Inductor | Inductor | L1, L2 | Inductor | 2
HDR1X2 | Output | Header 2 | P1 | Header, 2-Pin | 1
HDR1X2 | Channel 1 | Header 2 | P2, P4, P7, P8, P10, P11 | Header, 2-Pin | 6
HDR1X2 | GND | Header 2 | P3 | Header, 2-Pin | 1
HDR1X4 | DC IN + 6V | Header 4 | P5 | Header, 4-Pin | 1
ece-BNC_ROUND | BNCROUND | BNCROUND | P6, P9 | BNC Round Socket | 2
ECE-RESC1608-0603SM | 100K | RES000162 | R1, R6, R12, R13 | RES CER 100K 1608 SM | 4
ECE-RESC1608-0603SM | 47R | RES000122 | R2, R7 | RES CER 47R 1608 SM | 2
ECE-RESC1608-0603SM | 1K | RES000138 | R3, R8 | RES CER 1K 1608 SM | 2
ECE-RESC1608-0603SM | 220K | RES000166 | R4, R5, R9, R10, R11 | RES CER 220K 1608 SM | 5
ECE-RESC1608-0603SM | 470R | RES000134 | R14 | RES CER 470R 1608 SM | 1
ECE-RESC1608-0603SM | 470K | RES000170 | R15 | RES CER 470K 1608 SM | 1
ECE-RESC1608-0603SM | 47K | RES000158 | R16 | RES CER 47K 1608 SM | 1
ECE-RESC1608-0603SM | 10K | RES000150 | R17, R18 | RES CER 10K 1608 SM | 2
ECE-RESC1608-0603SM | 56K | RES000159 | R19, R20 | RES CER 56K 1608 SM | 2
S8_N | LT1167 | LT1167 | U1, U2 | Instrumentation amplifier, Low noise | 2
S8_N | LT1678 | LT1632CS8 | U3, U4 | 45MHz, 45V/µs, Dual Rail-to-Rail Input and Output Precision Operational Amplifier | 2
 |  |  |  |  | 57
Approved |  | Notes

Sheet: Project Information
Project Full Path | Z:\npat025\Documents\research\schematics\low_noise_amp_IA_opamp\lna_ia_opamp.PrjPcb
Project Filename | lna_ia_opamp.PrjPcb
Variant Name | None
Data-Source Filename | lna_ia_opamp.PrjPcb
Data-Source Full Path | Z:\npat025\Documents\research\schematics\low_noise_amp_IA_opamp\lna_ia_opamp.PrjPcb
Title | <Parameter Title not found>
Total Quantity | 57
Report Time | 9:22:28 AM
Report Date | 3/7/2016
Report Date & Tine | 3/7/2016 9:22:28 AM
Output Name | Bill of Materials
Output Type | BOM_PartType
Output Generator Name | BOM
Output Generator Description | Bill of Materials
