Arnesh-sharma/P4P_Project-130/Testing Data/For Report/archieved/Larger_distance/5IA_Setup_large_dist.jpg

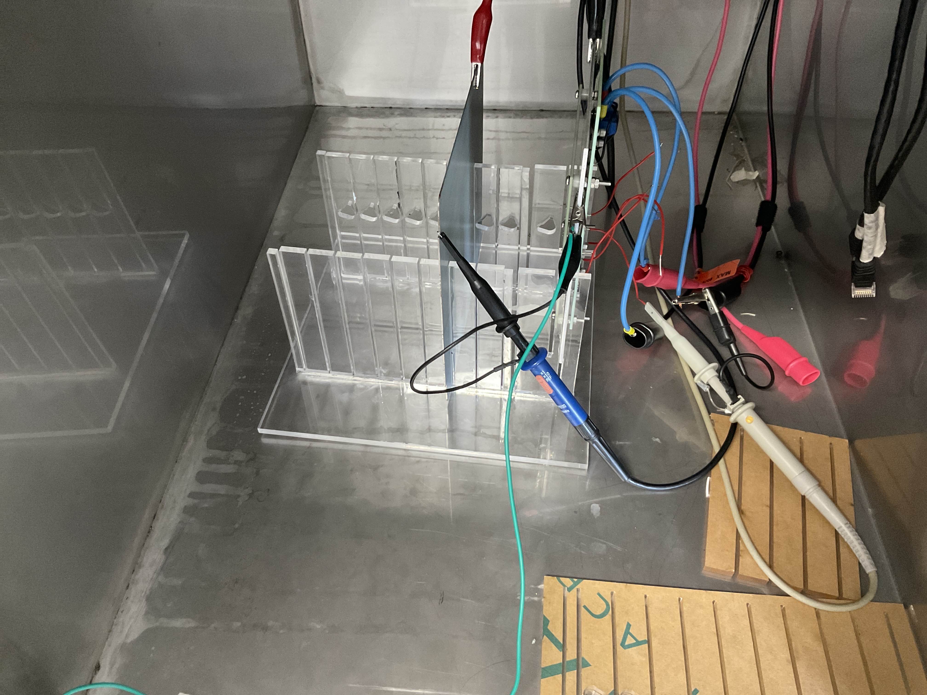
Testing Data/For Report/archieved/Larger_distance/5IA_Setup_large_dist.jpg
