Arnesh-sharma/P4P_Project-130/Testing Data/For Report/BeeSpy5_Setup.jpg

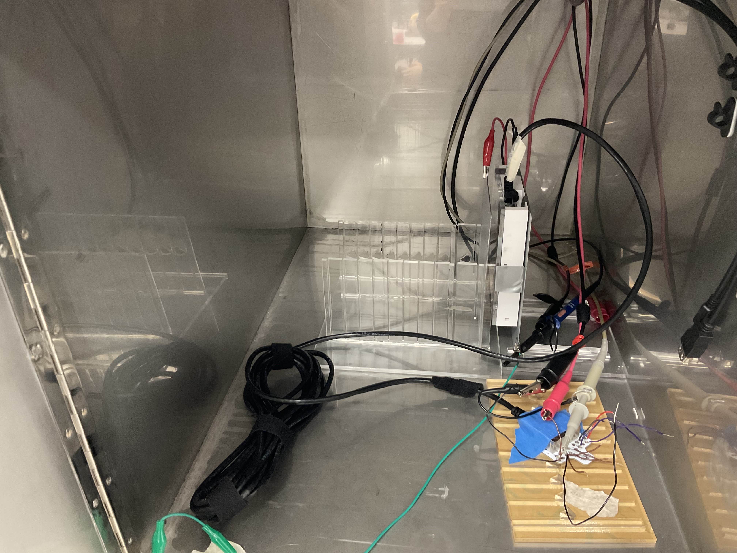
Testing Data/For Report/BeeSpy5_Setup.jpg
