Arnesh-sharma/P4P_Project-130/Testing Data/For Report/Electret_Setup(2).jpg

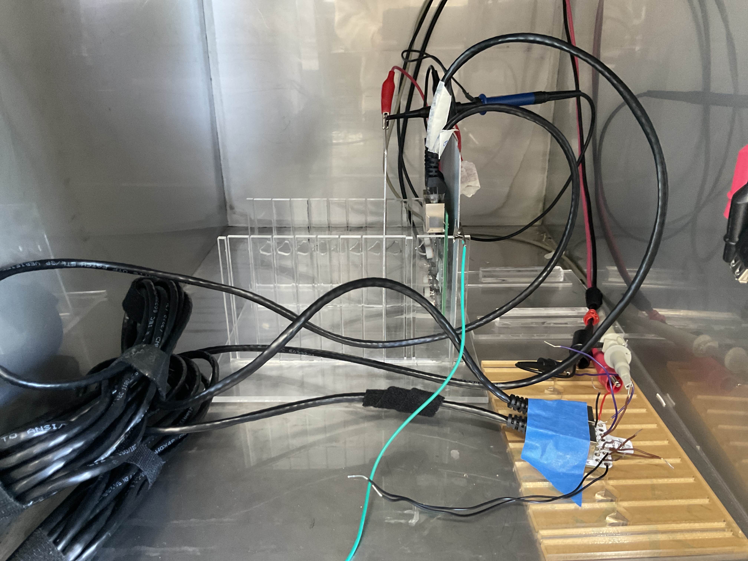
Testing Data/For Report/Electret_Setup(2).jpg
