Arnesh-sharma/P4P_Project-130/Testing Data/For Report/Electret_Setup.jpg

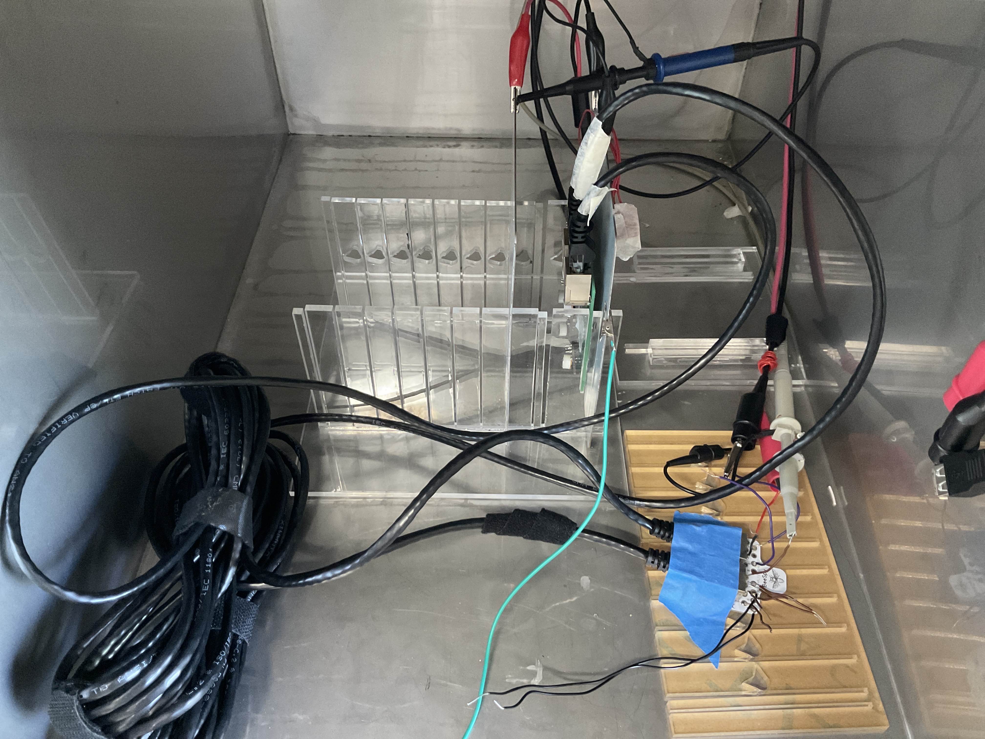
Testing Data/For Report/Electret_Setup.jpg
