Arnesh-sharma/P4P_Project-130/Testing Data/For Report/IA Sensors/IA 5 Sensors/5IA_Setup(2).jpg

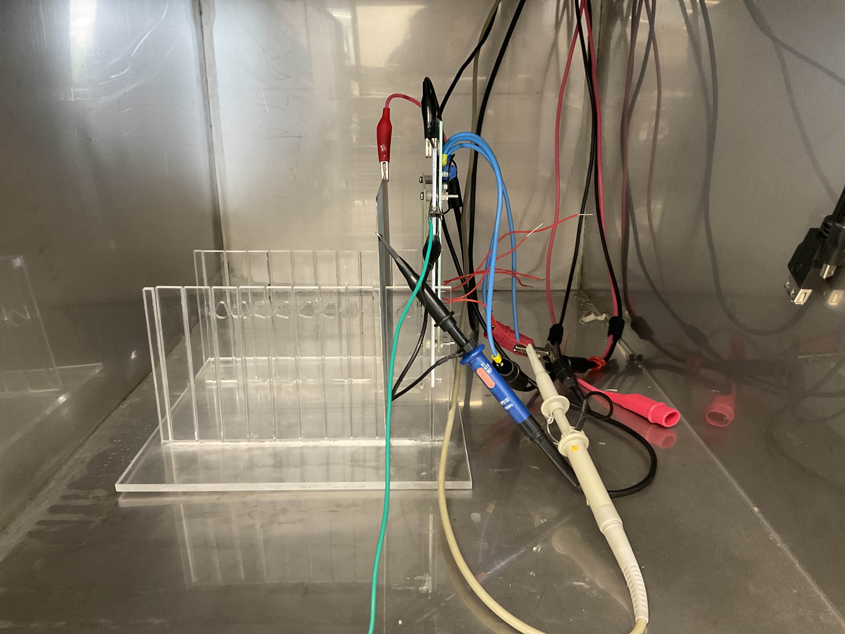
Testing Data/For Report/IA Sensors/IA 5 Sensors/5IA_Setup(2).jpg
