Arnesh-sharma/P4P_Project-130/Testing Data/25_07_25/BeeSpy_Electret_Sensors/electret1.csv

x-axis | 1
second | Volt
-10.00000E-03 | +17.89063E-03
-9.98000E-03 | -99.29687E-03
-9.96000E-03 | -220.39062E-03
-9.94000E-03 | -335.62500E-03
-9.92000E-03 | -450.85937E-03
-9.90000E-03 | -559.25781E-03
-9.88000E-03 | -655.93750E-03
-9.86000E-03 | -742.85156E-03
-9.84000E-03 | -815.11719E-03
-9.82000E-03 | -879.57031E-03
-9.80000E-03 | -927.42187E-03
-9.78000E-03 | -962.57812E-03
-9.76000E-03 | -982.10937E-03
-9.74000E-03 | -986.01562E-03
-9.72000E-03 | -975.27344E-03
-9.70000E-03 | -947.92969E-03
-9.68000E-03 | -906.91406E-03
-9.66000E-03 | -850.27344E-03
-9.64000E-03 | -781.91406E-03
-9.62000E-03 | -703.78906E-03
-9.60000E-03 | -611.01562E-03
-9.58000E-03 | -509.45312E-03
-9.56000E-03 | -396.17187E-03
-9.54000E-03 | -281.91406E-03
-9.52000E-03 | -162.77344E-03
-9.50000E-03 | -43.63281E-03
-9.48000E-03 | +71.60156E-03
-9.46000E-03 | +191.71875E-03
-9.44000E-03 | +306.95313E-03
-9.42000E-03 | +415.35156E-03
-9.40000E-03 | +518.86719E-03
-9.38000E-03 | +614.57031E-03
-9.36000E-03 | +697.57813E-03
-9.34000E-03 | +768.86719E-03
-9.32000E-03 | +825.50781E-03
-9.30000E-03 | +870.42969E-03
-9.28000E-03 | +901.67969E-03
-9.26000E-03 | +920.23438E-03
-9.24000E-03 | +924.14063E-03
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
