Arnesh-sharma/P4P_Project-130/Testing Data/25_07_25/BeeSpy_Electret_Sensors/electret3.csv

x-axis | 1
second | Volt
-10.00000E-03 | +9.76562E-03
-9.98000E-03 | -123.04688E-03
-9.96000E-03 | -257.81250E-03
-9.94000E-03 | -387.69531E-03
-9.92000E-03 | -517.57812E-03
-9.90000E-03 | -635.74219E-03
-9.88000E-03 | -742.18750E-03
-9.86000E-03 | -835.93750E-03
-9.84000E-03 | -919.92187E-03
-9.82000E-03 | -990.23437E-03
-9.80000E-03 | -1.04589844E+00
-9.78000E-03 | -1.08300781E+00
-9.76000E-03 | -1.10351562E+00
-9.74000E-03 | -1.10742188E+00
-9.72000E-03 | -1.09277344E+00
-9.70000E-03 | -1.06250000E+00
-9.68000E-03 | -1.01367188E+00
-9.66000E-03 | -949.21875E-03
-9.64000E-03 | -871.09375E-03
-9.62000E-03 | -780.27344E-03
-9.60000E-03 | -679.68750E-03
-9.58000E-03 | -565.42969E-03
-9.56000E-03 | -440.42969E-03
-9.54000E-03 | -309.57031E-03
-9.52000E-03 | -177.73438E-03
-9.50000E-03 | -42.96875E-03
-9.48000E-03 | +85.93750E-03
-9.46000E-03 | +220.70312E-03
-9.44000E-03 | +349.60937E-03
-9.42000E-03 | +471.67969E-03
-9.40000E-03 | +588.86719E-03
-9.38000E-03 | +693.35937E-03
-9.36000E-03 | +786.13281E-03
-9.34000E-03 | +862.30469E-03
-9.32000E-03 | +925.78125E-03
-9.30000E-03 | +977.53906E-03
-9.28000E-03 | +1.01269531E+00
-9.26000E-03 | +1.03222656E+00
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
