Arnesh-sharma/P4P_Project-130/Testing Data/25_07_25/BeeSpy_Electret_Sensors/electret5.csv

x-axis | 1
second | Volt
-10.00000E-03 | +19.53125E-03
-9.98000E-03 | -71.28906E-03
-9.96000E-03 | -166.99219E-03
-9.94000E-03 | -260.74219E-03
-9.92000E-03 | -348.63281E-03
-9.90000E-03 | -434.57031E-03
-9.88000E-03 | -514.64844E-03
-9.86000E-03 | -583.98437E-03
-9.84000E-03 | -646.48437E-03
-9.82000E-03 | -697.26562E-03
-9.80000E-03 | -736.32812E-03
-9.78000E-03 | -763.67187E-03
-9.76000E-03 | -778.32031E-03
-9.74000E-03 | -783.20312E-03
-9.72000E-03 | -776.36719E-03
-9.70000E-03 | -760.74219E-03
-9.68000E-03 | -730.46875E-03
-9.66000E-03 | -688.47656E-03
-9.64000E-03 | -635.74219E-03
-9.62000E-03 | -573.24219E-03
-9.60000E-03 | -501.95313E-03
-9.58000E-03 | -419.92188E-03
-9.56000E-03 | -333.98438E-03
-9.54000E-03 | -245.11719E-03
-9.52000E-03 | -151.36719E-03
-9.50000E-03 | -55.66406E-03
-9.48000E-03 | +34.17969E-03
-9.46000E-03 | +126.95312E-03
-9.44000E-03 | +221.67969E-03
-9.42000E-03 | +309.57031E-03
-9.40000E-03 | +389.64844E-03
-9.38000E-03 | +466.79687E-03
-9.36000E-03 | +536.13281E-03
-9.34000E-03 | +596.67969E-03
-9.32000E-03 | +647.46094E-03
-9.30000E-03 | +685.54687E-03
-9.28000E-03 | +712.89062E-03
-9.26000E-03 | +730.46875E-03
-9.24000E-03 | +736.32812E-03
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
