Arnesh-sharma/P4P_Project-130/Testing Data/25_07_25/BeeSpy_Electret_Sensors/electret6.csv

x-axis | 1
second | Volt
-10.00000E-03 | +17.57812E-03
-9.98000E-03 | -63.47656E-03
-9.96000E-03 | -150.39062E-03
-9.94000E-03 | -235.35156E-03
-9.92000E-03 | -314.45312E-03
-9.90000E-03 | -390.62500E-03
-9.88000E-03 | -463.86719E-03
-9.86000E-03 | -529.29687E-03
-9.84000E-03 | -583.98437E-03
-9.82000E-03 | -630.85937E-03
-9.80000E-03 | -667.96875E-03
-9.78000E-03 | -694.33594E-03
-9.76000E-03 | -710.93750E-03
-9.74000E-03 | -715.82031E-03
-9.72000E-03 | -708.98438E-03
-9.70000E-03 | -692.38281E-03
-9.68000E-03 | -665.03906E-03
-9.66000E-03 | -626.95313E-03
-9.64000E-03 | -579.10156E-03
-9.62000E-03 | -523.43750E-03
-9.60000E-03 | -457.03125E-03
-9.58000E-03 | -383.78906E-03
-9.56000E-03 | -307.61719E-03
-9.54000E-03 | -227.53906E-03
-9.52000E-03 | -142.57813E-03
-9.50000E-03 | -55.66406E-03
-9.48000E-03 | +24.41406E-03
-9.46000E-03 | +108.39844E-03
-9.44000E-03 | +194.33594E-03
-9.42000E-03 | +274.41406E-03
-9.40000E-03 | +347.65625E-03
-9.38000E-03 | +416.01562E-03
-9.36000E-03 | +478.51562E-03
-9.34000E-03 | +535.15625E-03
-9.32000E-03 | +581.05469E-03
-9.30000E-03 | +619.14062E-03
-9.28000E-03 | +645.50781E-03
-9.26000E-03 | +660.15625E-03
-9.24000E-03 | +665.03906E-03
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
