Arnesh-sharma/P4P_Project-130/Raw_Data/electret stuff/scope_0.csv

x-axis | 1 | 2
second | Volt | Volt
-100.0000E-03 | +1.7812500E+00 | +1.8062500E+00
-99.8000E-03 | +1.7031250E+00 | +1.7437500E+00
-99.6000E-03 | +1.6406250E+00 | +1.6656250E+00
-99.4000E-03 | +1.5781250E+00 | +1.5718750E+00
-99.2000E-03 | +1.5156250E+00 | +1.5093750E+00
-99.0000E-03 | +1.4375000E+00 | +1.4000000E+00
-98.8000E-03 | +1.3593750E+00 | +1.3062500E+00
-98.6000E-03 | +1.2968750E+00 | +1.2281250E+00
-98.4000E-03 | +1.2031250E+00 | +1.1500000E+00
-98.2000E-03 | +1.1406250E+00 | +1.0718750E+00
-98.0000E-03 | +1.0781250E+00 | +993.7500E-03
-97.8000E-03 | +1.0312500E+00 | +946.8750E-03
-97.6000E-03 | +968.7500E-03 | +884.3750E-03
-97.4000E-03 | +937.5000E-03 | +821.8750E-03
-97.2000E-03 | +906.2500E-03 | +790.6250E-03
-97.0000E-03 | +875.0000E-03 | +775.0000E-03
-96.8000E-03 | +890.6250E-03 | +759.3750E-03
-96.6000E-03 | +859.3750E-03 | +743.7500E-03
-96.4000E-03 | +859.3750E-03 | +743.7500E-03
-96.2000E-03 | +890.6250E-03 | +775.0000E-03
-96.0000E-03 | +921.8750E-03 | +806.2500E-03
-95.8000E-03 | +953.1250E-03 | +837.5000E-03
-95.6000E-03 | +984.3750E-03 | +868.7500E-03
-95.4000E-03 | +1.0625000E+00 | +915.6250E-03
-95.2000E-03 | +1.1093750E+00 | +1.0093750E+00
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
