Arnesh-sharma/P4P_Project-130/Raw_Data/electret stuff/scope_1.csv

x-axis | 1 | 2
second | Volt | Volt
-1.000000E+00 | +1.340000E+00 | +1.286250E+00
-998.000E-03 | +1.315000E+00 | +1.248750E+00
-996.000E-03 | +1.290000E+00 | +1.205000E+00
-994.000E-03 | +1.290000E+00 | +1.217500E+00
-992.000E-03 | +1.290000E+00 | +1.205000E+00
-990.000E-03 | +1.302500E+00 | +1.217500E+00
-988.000E-03 | +1.308750E+00 | +1.236250E+00
-986.000E-03 | +1.333750E+00 | +1.261250E+00
-984.000E-03 | +1.371250E+00 | +1.298750E+00
-982.000E-03 | +1.390000E+00 | +1.323750E+00
-980.000E-03 | +1.427500E+00 | +1.367500E+00
-978.000E-03 | +1.477500E+00 | +1.430000E+00
-976.000E-03 | +1.527500E+00 | +1.473750E+00
-974.000E-03 | +1.571250E+00 | +1.542500E+00
-972.000E-03 | +1.608750E+00 | +1.580000E+00
-970.000E-03 | +1.652500E+00 | +1.636250E+00
-968.000E-03 | +1.690000E+00 | +1.686250E+00
-966.000E-03 | +1.715000E+00 | +1.711250E+00
-964.000E-03 | +1.727500E+00 | +1.742500E+00
-962.000E-03 | +1.746250E+00 | +1.755000E+00
-960.000E-03 | +1.746250E+00 | +1.755000E+00
-958.000E-03 | +1.740000E+00 | +1.761250E+00
-956.000E-03 | +1.733750E+00 | +1.748750E+00
-954.000E-03 | +1.721250E+00 | +1.730000E+00
-952.000E-03 | +1.683750E+00 | +1.692500E+00
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
