Arnesh-sharma/P4P_Project-130/Raw_Data/electret stuff/scope_2.csv

x-axis | 1 | 2
second | Volt | Volt
-50.000E-03 | +1.065625E+00 | +934.375E-03
-49.900E-03 | +1.159375E+00 | +1.075000E+00
-49.800E-03 | +1.268750E+00 | +1.168750E+00
-49.700E-03 | +1.393750E+00 | +1.309375E+00
-49.600E-03 | +1.503125E+00 | +1.434375E+00
-49.500E-03 | +1.628125E+00 | +1.559375E+00
-49.400E-03 | +1.737500E+00 | +1.700000E+00
-49.300E-03 | +1.831250E+00 | +1.809375E+00
-49.200E-03 | +1.940625E+00 | +1.918750E+00
-49.100E-03 | +2.003125E+00 | +2.012500E+00
-49.000E-03 | +2.050000E+00 | +2.059375E+00
-48.900E-03 | +2.081250E+00 | +2.121875E+00
-48.800E-03 | +2.096875E+00 | +2.153125E+00
-48.700E-03 | +2.096875E+00 | +2.137500E+00
-48.600E-03 | +2.081250E+00 | +2.106250E+00
-48.500E-03 | +2.018750E+00 | +2.075000E+00
-48.400E-03 | +1.956250E+00 | +2.012500E+00
-48.300E-03 | +1.878125E+00 | +1.918750E+00
-48.200E-03 | +1.800000E+00 | +1.793750E+00
-48.100E-03 | +1.675000E+00 | +1.684375E+00
-48.000E-03 | +1.534375E+00 | +1.543750E+00
-47.900E-03 | +1.425000E+00 | +1.418750E+00
-47.800E-03 | +1.315625E+00 | +1.278125E+00
-47.700E-03 | +1.190625E+00 | +1.153125E+00
-47.600E-03 | +1.112500E+00 | +1.028125E+00
-47.500E-03 | +1.003125E+00 | +950.000E-03
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
