Arnesh-sharma/P4P_Project-130/Testing Data/25_07_25/JFET_Sensors/JFET_v2.csv

x-axis | 1
second | Volt
-5.00000E-03 | +4.00625E-03
-4.99000E-03 | +4.04531E-03
-4.98000E-03 | +4.04531E-03
-4.97000E-03 | +4.12344E-03
-4.96000E-03 | +4.08437E-03
-4.95000E-03 | +4.04531E-03
-4.94000E-03 | +3.88906E-03
-4.93000E-03 | +3.88906E-03
-4.92000E-03 | +3.73281E-03
-4.91000E-03 | +3.57656E-03
-4.90000E-03 | +3.38125E-03
-4.89000E-03 | +3.22500E-03
-4.88000E-03 | +2.91250E-03
-4.87000E-03 | +2.56094E-03
-4.86000E-03 | +2.36562E-03
-4.85000E-03 | +2.09219E-03
-4.84000E-03 | +1.66250E-03
-4.83000E-03 | +1.50625E-03
-4.82000E-03 | +1.11562E-03
-4.81000E-03 | +959.37E-06
-4.80000E-03 | +529.69E-06
-4.79000E-03 | +256.25E-06
-4.78000E-03 | -173.44E-06
-4.77000E-03 | -446.87E-06
-4.76000E-03 | -915.62E-06
-4.75000E-03 | -1.30625E-03
-4.74000E-03 | -1.57969E-03
-4.73000E-03 | -2.12656E-03
-4.72000E-03 | -2.51719E-03
-4.71000E-03 | -2.98594E-03
-4.70000E-03 | -3.41562E-03
-4.69000E-03 | -3.80625E-03
-4.68000E-03 | -4.31406E-03
-4.67000E-03 | -4.70469E-03
-4.66000E-03 | -5.13437E-03
-4.65000E-03 | -5.52500E-03
-4.64000E-03 | -5.91562E-03
-4.63000E-03 | -6.26719E-03
-4.62000E-03 | -6.57969E-03
-4.61000E-03 | -6.85312E-03
-4.60000E-03 | -7.24375E-03
-4.59000E-03 | -7.63437E-03
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
