Arnesh-sharma/P4P_Project-130/Experimental_cap_sense/image.png

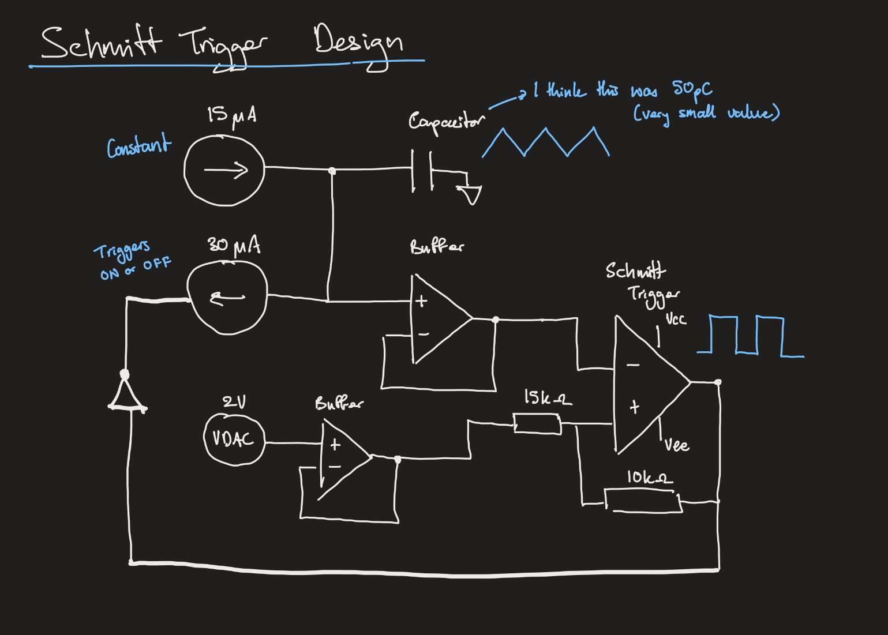
Experimental_cap_sense/image.png
