Arnesh-sharma/P4P_Project-130/Matlab Code/electret_point_test.png

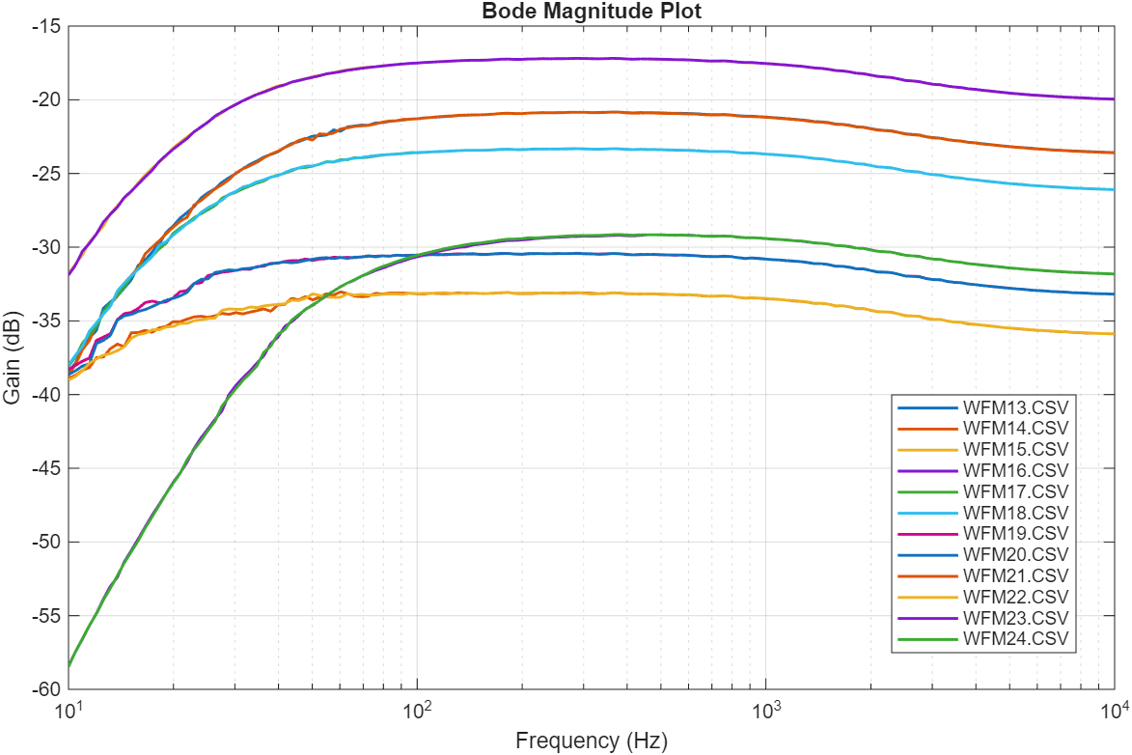
Matlab Code/electret_point_test.png
