Arnesh-sharma/P4P_Project-130/Matlab Code/IA_Point_test.png

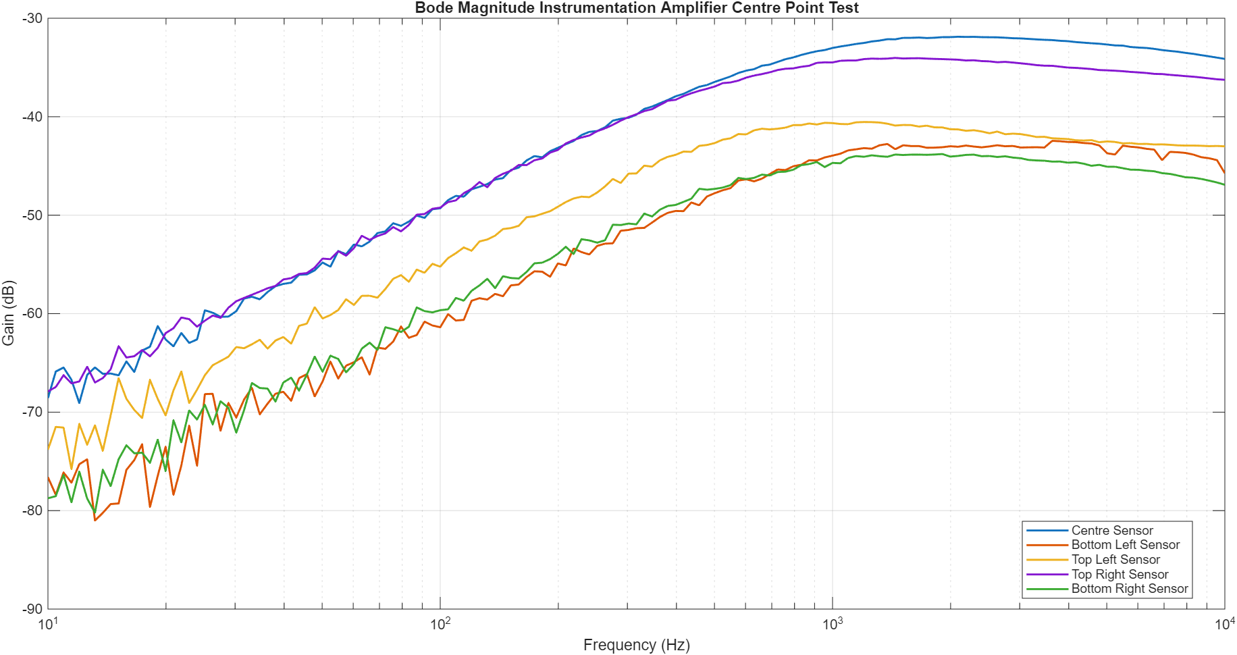
Matlab Code/IA_Point_test.png
