Arnesh-sharma/P4P_Project-130/Matlab Code/jfet_point_test.png

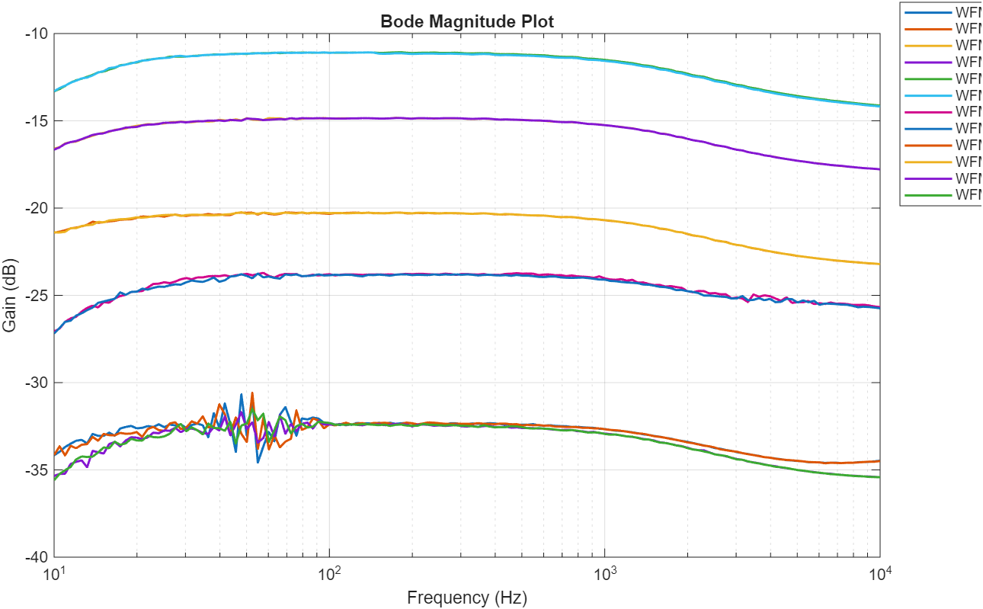
Matlab Code/jfet_point_test.png
