Arnesh-sharma/P4P_Project-130/Matlab Code/singles_jfet_plate_test.png

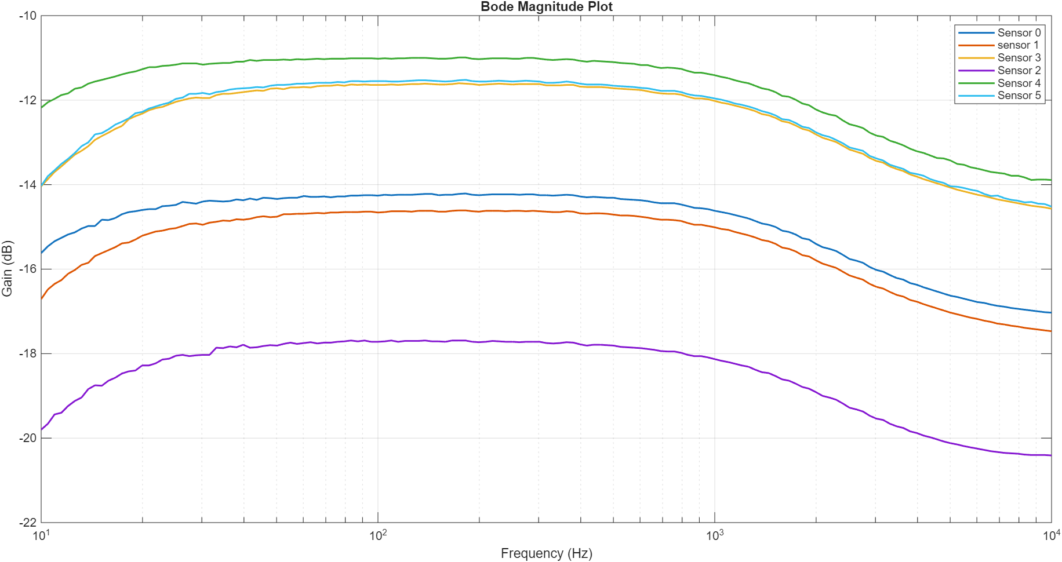
Matlab Code/singles_jfet_plate_test.png
