Arnesh-sharma/P4P_Project-130/Testing Data/25_07_25/BeeSpy_Electret_Sensors/BeeSpy_Electrets.jpg

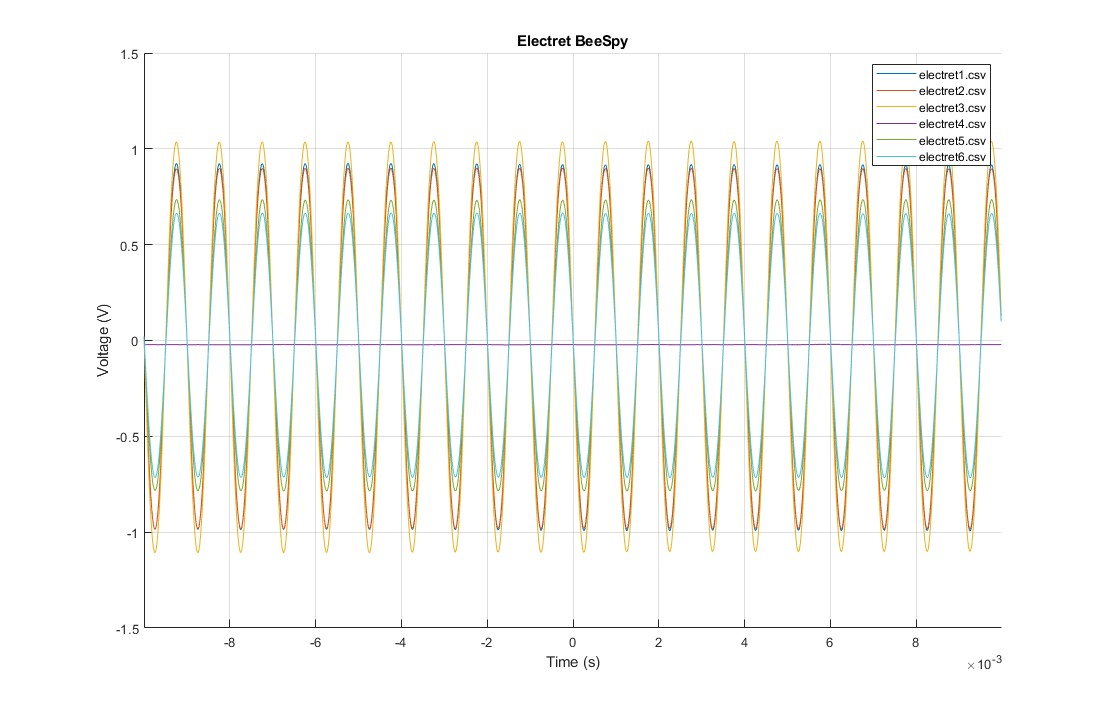
Testing Data/25_07_25/BeeSpy_Electret_Sensors/BeeSpy_Electrets.jpg
