Arnesh-sharma/P4P_Project-130/Testing Data/25_07_25/JFET_Sensors/JFET_sensors.jpg

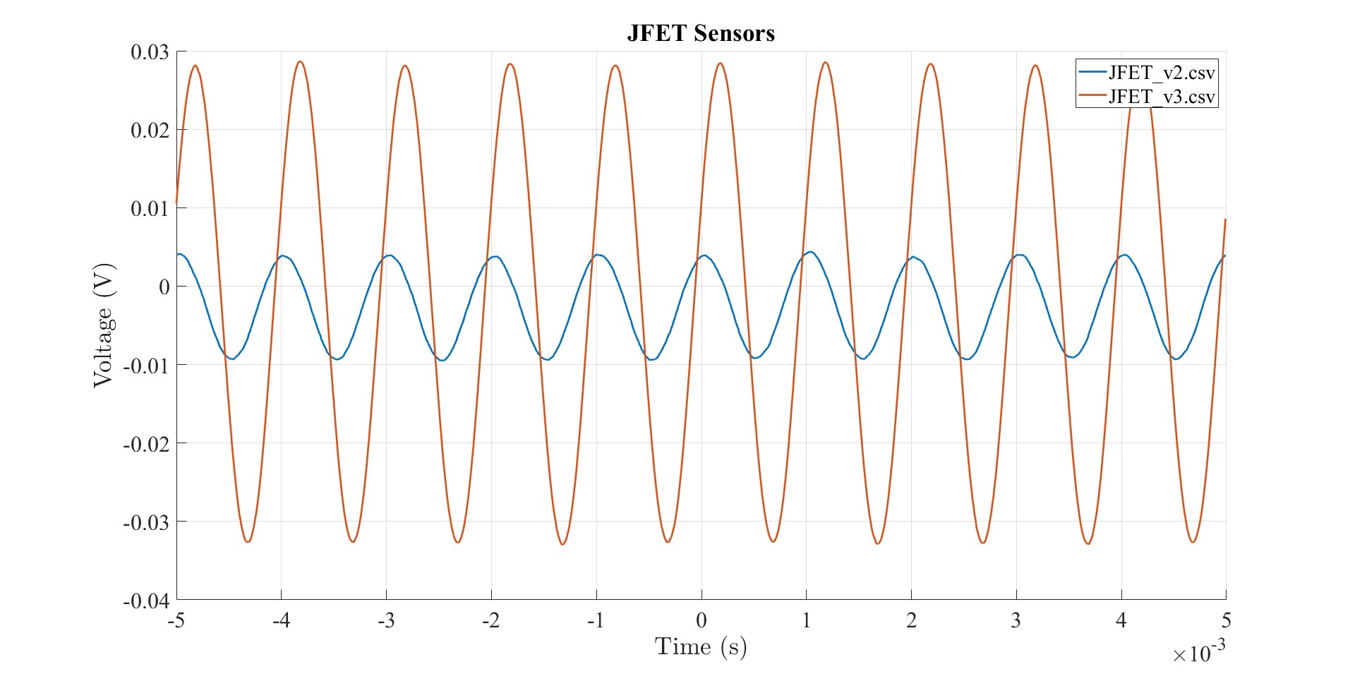
Testing Data/25_07_25/JFET_Sensors/JFET_sensors.jpg
