Arnesh-sharma/P4P_Project-130/Testing Data/FET_Data/FET_CH1_Bodes/IMG_1727.jpg

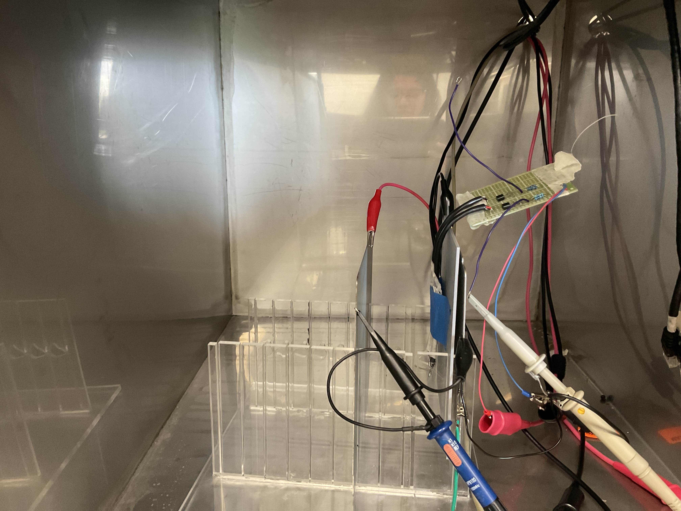
Testing Data/FET_Data/FET_CH1_Bodes/IMG_1727.jpg
