Arnesh-sharma/P4P_Project-130/PCBs/low_noise_amp/low_noise_16ch/lna_16ch_old.pdf

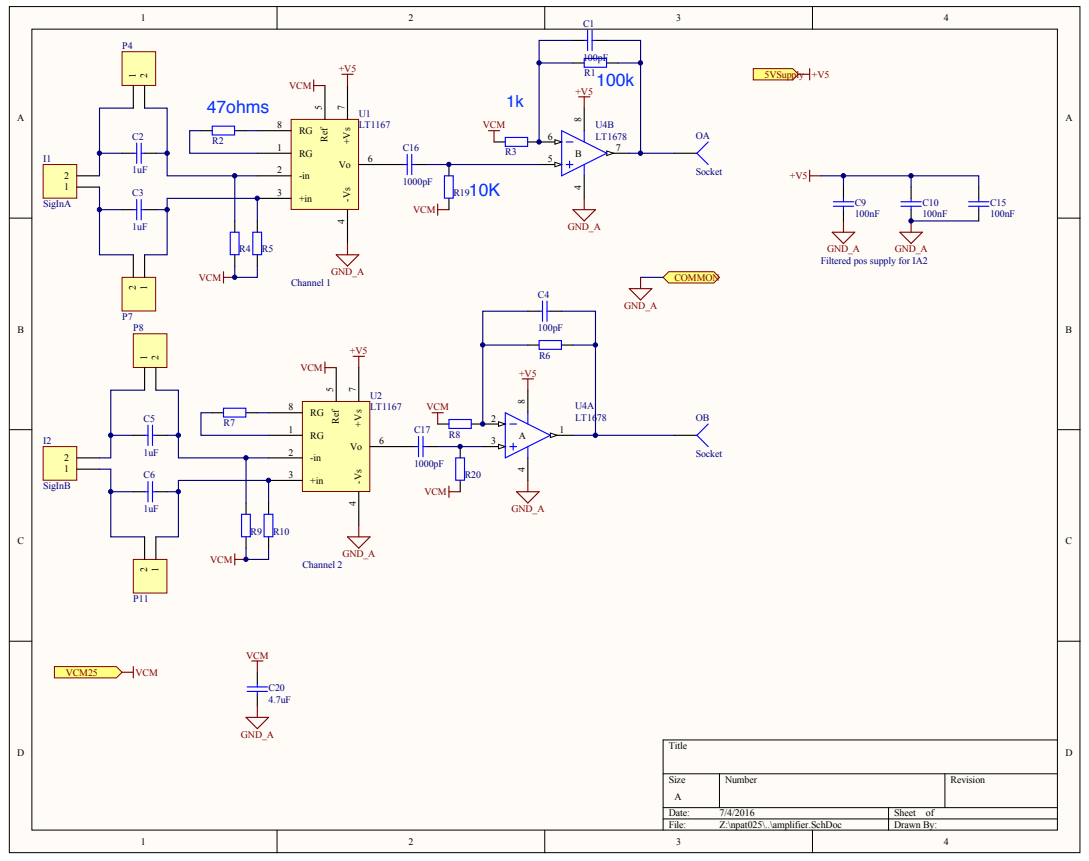
[picture p111: page 1]

Filtered pos supply for IA2

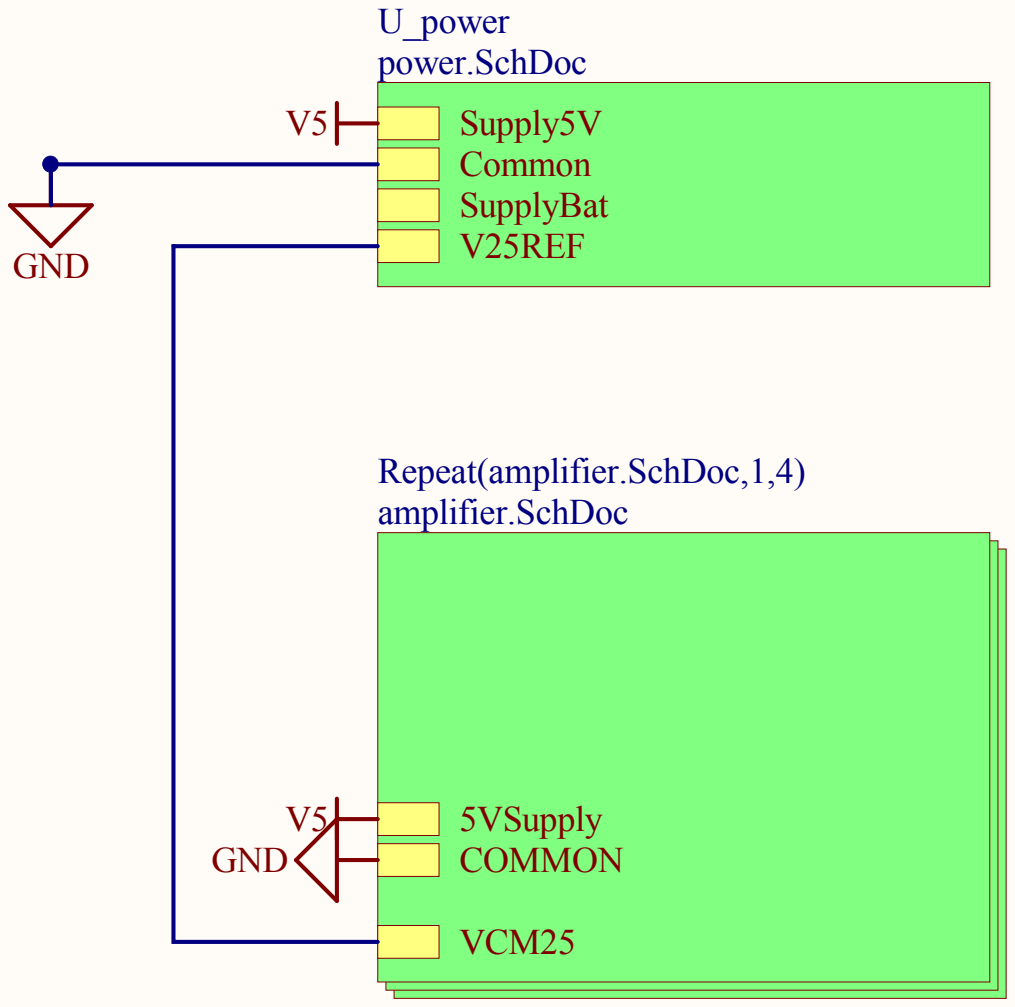
[picture p112: page 2]

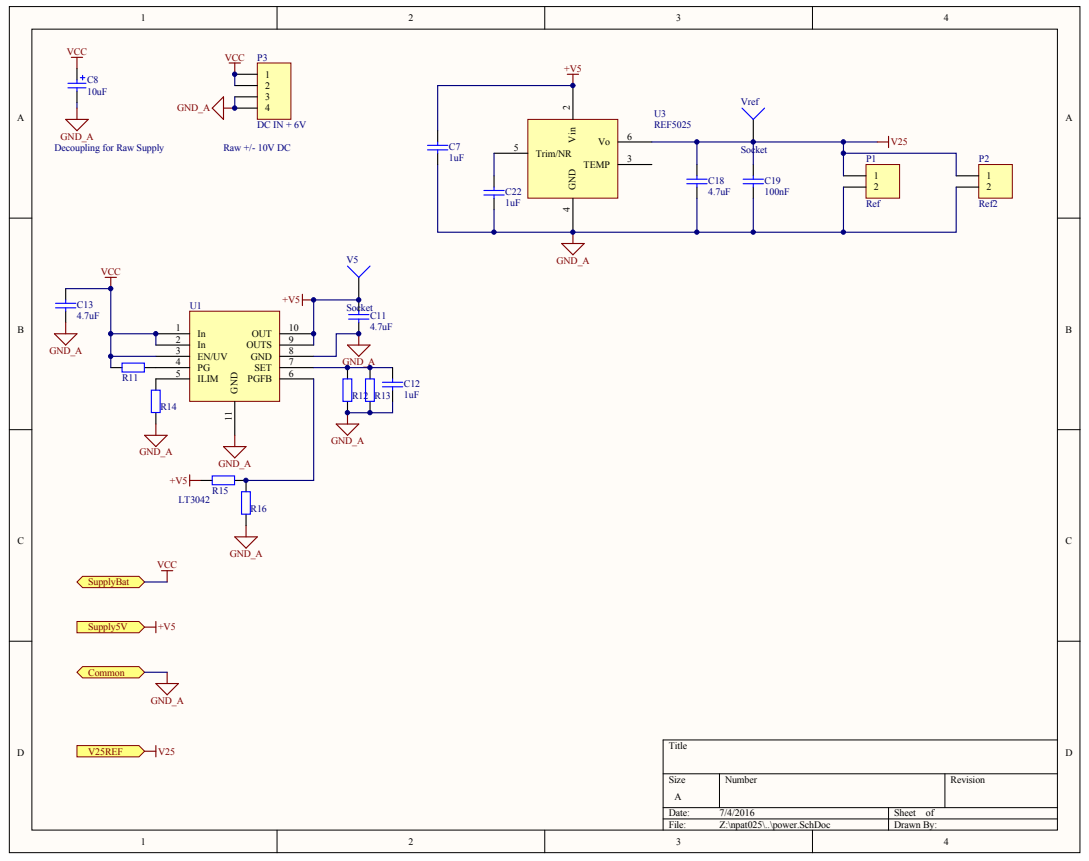
[picture p113: page 3]

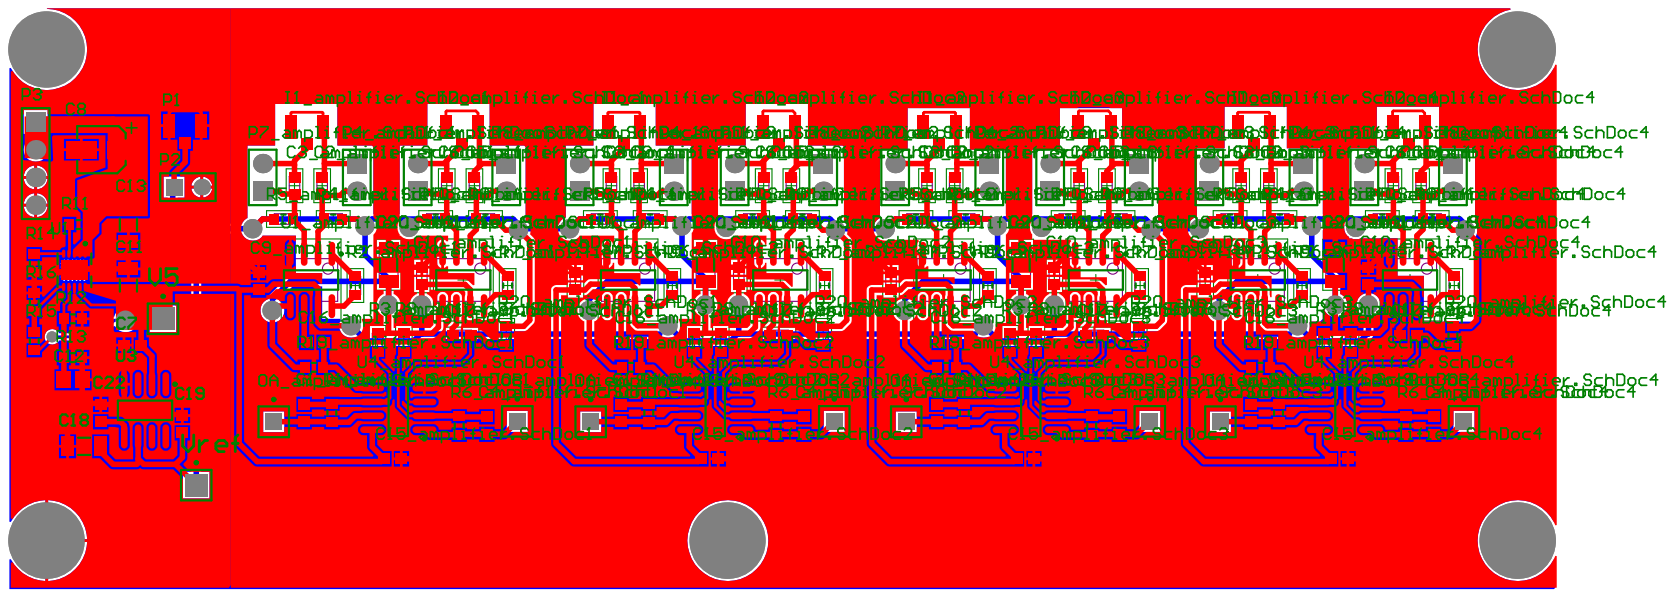
[picture p114: page 4]

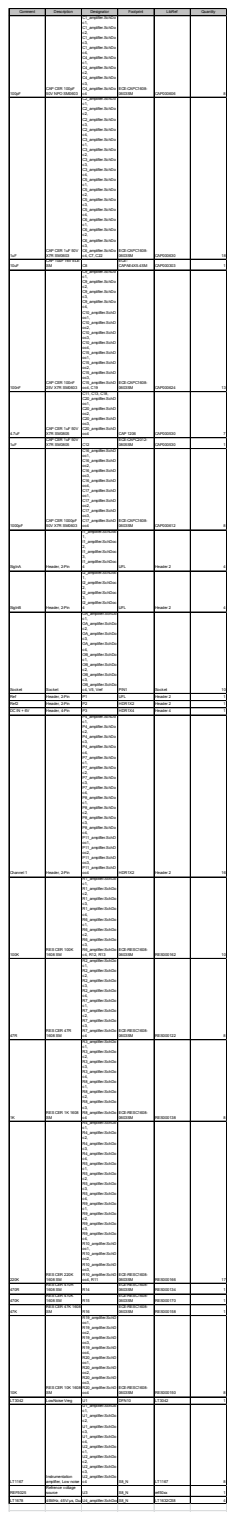
[picture p115: page 5]

Comment 100pF | Description CAP CER 100pF 50V NPO SM0603 | C1_amplifier.SchDo Designator c1, C1_amplifier.SchDo c2, C1_amplifier.SchDo c3, C1_amplifier.SchDo c4, C4_amplifier.SchDo c1, C4_amplifier.SchDo c2, C4_amplifier.SchDo c3, C4_amplifier.SchDo c4 | Footprint ECE-CAPC1608-0603SM | LibRef CAP000606 | Quantity | 8

1uF | CAP CER 1uF 50V X7R SM0603 | c1, C2_amplifier.SchDo C2_amplifier.SchDo c2, C2_amplifier.SchDo c3, C2_amplifier.SchDo c4, C3_amplifier.SchDo c1, C3_amplifier.SchDo c2, C3_amplifier.SchDo c3, C3_amplifier.SchDo c4, C5_amplifier.SchDo c1, C5_amplifier.SchDo c2, C5_amplifier.SchDo c3, C5_amplifier.SchDo c4, C6_amplifier.SchDo c1, C6_amplifier.SchDo c2, C6_amplifier.SchDo c3, C6_amplifier.SchDo c4, C7, C22 | ECE-CAPC1608-0603SM | CAP000630 | 18

10uF | CAP 10uF 16V ELE SM | C8 | ECE-CAPAE4X5.4SM | CAP000303 | | 1

100nF | CAP CER 100nF 25V X7R SM0603 | C9_amplifier.SchDo c1, C9_amplifier.SchDo c2, C9_amplifier.SchDo c3, C9_amplifier.SchDo c4, C10_amplifier.SchD oc1, C10_amplifier.SchD oc2, C10_amplifier.SchD oc3, C10_amplifier.SchD oc4, C15_amplifier.SchD oc1, C15_amplifier.SchD oc2, C15_amplifier.SchD oc3, C15_amplifier.SchD oc4, C19 C11, C13, C18, | ECE-CAPC1608-0603SM | CAP000624 | 13

4.7uF | CAP CER 1uF 50V X7R SM0805 | C20_amplifier.SchD oc1, C20_amplifier.SchD oc2, C20_amplifier.SchD oc3, C20_amplifier.SchD oc4 | CAP 1206 | CAP000530 | | 7

1uF | CAP CER 1uF 50V X7R SM0805 | C12 | ECE-CAPC2012-0805SM | CAP000530 | | 1

1000pF | CAP CER 1000pF 50V X7R SM0603 | C16_amplifier.SchD oc1, C16_amplifier.SchD oc2, C16_amplifier.SchD oc3, C16_amplifier.SchD oc4, C17_amplifier.SchD oc1, C17_amplifier.SchD oc2, C17_amplifier.SchD oc3, C17_amplifier.SchD oc4 | ECE-CAPC1608-0603SM | CAP000612 | | 8

SigInA | Header, 2-Pin | I1_amplifier.SchDoc 1, I1_amplifier.SchDoc 2, I1_amplifier.SchDoc 3, I1_amplifier.SchDoc 4 | UFL | Header 2 | | 4

SigInB | Header, 2-Pin | I2_amplifier.SchDoc 1, I2_amplifier.SchDoc 2, I2_amplifier.SchDoc 3, I2_amplifier.SchDoc 4 | UFL | Header 2 | | 4

Socket | Socket | OA_amplifier.SchDo c1, OA_amplifier.SchDo c2, OA_amplifier.SchDo c3, OA_amplifier.SchDo c4, OB_amplifier.SchDo c1, OB_amplifier.SchDo c2, OB_amplifier.SchDo c3, OB_amplifier.SchDo c4, V5, Vref | PIN1 | Socket | 10

Ref | Header, 2-Pin | P1 | UFL | Header 2 | | 1
Ref2 | Header, 2-Pin | P2 | HDR1X2 | Header 2 | | 1
DC IN a 6V | Header, 4-Pin | P3 | HDR1X4 | Header 4 | | 1
Channel 1 | Header, 2-Pin | P4_amplifier.SchDo c1, P4_amplifier.SchDo c2, P4_amplifier.SchDo c3, P4_amplifier.SchDo c4, P7_amplifier.SchDo c1, P7_amplifier.SchDo c2, P7_amplifier.SchDo c3, P7_amplifier.SchDo c4, P8_amplifier.SchDo c1, P8_amplifier.SchDo c2, P8_amplifier.SchDo c3, P8_amplifier.SchDo c4, P11_amplifier.SchD oc1, P11_amplifier.SchD oc2, P11_amplifier.SchD oc3, P11_amplifier.SchD oc4 | HDR1X2 | Header 2 | 16

100K | RES CER 100K 1608 SM | R1_amplifier.SchDo c1, R1_amplifier.SchDo c2, R1_amplifier.SchDo c3, R1_amplifier.SchDo c4, R6_amplifier.SchDo c1, R6_amplifier.SchDo c2, R6_amplifier.SchDo c3, R6_amplifier.SchDo c4, R12, R13 | ECE-RESC1608-0603SM | RES000162 | 10

47R | RES CER 47R 1608 SM | R2_amplifier.SchDo c1, R2_amplifier.SchDo c2, R2_amplifier.SchDo c3, R2_amplifier.SchDo c4, R7_amplifier.SchDo c1, R7_amplifier.SchDo c2, R7_amplifier.SchDo c3, R7_amplifier.SchDo c4 | ECE-RESC1608-0603SM | RES000122 | | 8

1K | RES CER 1K 1608 SM | R3_amplifier.SchDo c1, R3_amplifier.SchDo c2, R3_amplifier.SchDo c3, R3_amplifier.SchDo c4, R8_amplifier.SchDo c1, R8_amplifier.SchDo c2, R8_amplifier.SchDo c3, R8_amplifier.SchDo c4 R4_amplifier.SchDo | ECE-RESC1608-0603SM | RES000138 | | 8

220K | RES CER 220K 1608 SM | c1, R4_amplifier.SchDo c2, R4_amplifier.SchDo c3, R4_amplifier.SchDo c4, R5_amplifier.SchDo c1, R5_amplifier.SchDo c2, R5_amplifier.SchDo c3, R5_amplifier.SchDo c4, R9_amplifier.SchDo c1, R9_amplifier.SchDo c2, R9_amplifier.SchDo c3, R9_amplifier.SchDo c4, R10_amplifier.SchD oc1, R10_amplifier.SchD oc2, R10_amplifier.SchD oc3, R10_amplifier.SchD oc4, R11 | ECE-RESC1608-0603SM | RES000166 | 17

470R | RES CER 470R 1608 SM | R14 | ECE-RESC1608-0603SM | RES000134 | | 1

470K | RES CER 470K 1608 SM | R15 | ECE-RESC1608-0603SM | RES000170 | | 1

47K | RES CER 47K 1608 SM | R16 | ECE-RESC1608-0603SM | RES000158 | | 1

10K | RES CER 10K 1608 SM | R19_amplifier.SchD oc1, R19_amplifier.SchD oc2, R19_amplifier.SchD oc3, R19_amplifier.SchD oc4, R20_amplifier.SchD oc1, R20_amplifier.SchD oc2, R20_amplifier.SchD oc3, R20_amplifier.SchD oc4 | ECE-RESC1608-0603SM | RES000150 | | 8

LT3042 LT1167 | LowNoise Vreg Instrumentation amplifier, Low noise | U1 U1_amplifier.SchDo c1, U1_amplifier.SchDo c2, U1_amplifier.SchDo c3, U1_amplifier.SchDo c4, U2_amplifier.SchDo c1, U2_amplifier.SchDo c2, U2_amplifier.SchDo c3, U2_amplifier.SchDo c4 | DFN10 S8_N | LT3042 LT1167 | | 1 8

REF5025 | Refrence voltage source | U3 | S8_N | ref50xx | 1

LT1678 | 45MHz, 45V/ µs, DuaU4 _amplifier .SchDo cS 8_N | | | LT1 632C S8 | 4
