Arnesh-sharma/P4P_Project-130/Experimental_cap_sense/LT_SPICE/Schmitt_trigger.asc

C1: cap; 150nF
R1: res; 15k
R2: res; 10k
U1: UniversalOpAmp2
V1: voltage; 4.8
V2: voltage; 2
V3: voltage; SINE(1 3 1)
Named nets: vout, vref, 0, vcc, vin
.tran 0 100 0 0.01
Inverting schmitt trigger design
hysteresis at 3.5V and 0.5V
