Arnesh-sharma/P4P_Project-130/Experimental_cap_sense/LT_SPICE/seconds.asc

C1: cap; 12p
R1: res; 15k
R2: res; 15k
R4: res; 15k
R5: res; 1Meg
U1: TL082
V1: voltage; 5
V2: voltage; 5
V3: voltage; SINE(1 3 1)
Named nets: vout, vref, 0, vin, vcc
.tran 0 500u 0 0.01
Inverting schmitt trigger design
hysteresis at 3.5V and 0.5V
