Arnesh-sharma/P4P_Project-130/Experimental_cap_sense/LT_SPICE/Draft4.asc

C1: cap; 300n
C2: cap; 900n
C3: cap; 900n
C4: cap; 300n
C5: cap; 300n
C6: cap; 300n
C7: cap; 300n
C8: cap; 1000p
C9: cap; 1000p
C10: cap; 1000p
C11: cap; 1000p
C12: cap; 1000p
C13: cap; 1000p
C14: cap; 1000p
C15: cap; 1000p
D1: diode
D2: diode
D3: diode
D4: diode
D5: diode
D6: diode
D7: diode
D8: diode
D9: diode
D10: diode
D11: diode
D12: diode
D13: diode
D14: diode
D15: diode
Vin1: voltage; SINE(0 10 50)
Vin: voltage; SINE(0 10 50)
Named nets: Vo, Vo1, 0, o, V1, output
.tran 0 5 0 100
Sim settings
Half wave voltage doubler
full wave voltage doubler
4x multiplier
Cockcroft-Walton Multiplier
Voltage settings
