Arnesh-sharma/P4P_Project-130/Capsense_stuff/Cap_Sense.cydsn/CapSense_CSD_WithTuner01.cydsn/codegentemp/CapSense_CSD_AMuxCH0.h

/*******************************************************************************
* File Name: CapSense_CSD_AMuxCH0.h
* Version 3.50
*
*  Description:
*    This file contains the constants and function prototypes for the Analog
*    Multiplexer User Module CapSense_CSD_AMux.
*
*   Note:
*
********************************************************************************
* Copyright 2008-2012, Cypress Semiconductor Corporation.  All rights reserved.
* You may use this file only in accordance with the license, terms, conditions,
* disclaimers, and limitations in the end user license agreement accompanying
* the software package with which this file was provided.
*******************************************************************************/

#if !defined(CY_CAPSENSE_CSD_AMUX_CapSense_CSD_AMuxCH0_H)
#define CY_CAPSENSE_CSD_AMUX_CapSense_CSD_AMuxCH0_H

#include "cytypes.h"
#include "cyfitter.h"
#include "cyfitter_cfg.h"


/***************************************
*        Function Prototypes
***************************************/

void CapSense_CSD_AMuxCH0_Start(void);
void CapSense_CSD_AMuxCH0_Init(void);
void CapSense_CSD_AMuxCH0_Stop(void);
void CapSense_CSD_AMuxCH0_Select(uint8 channel) CYREENTRANT;
void CapSense_CSD_AMuxCH0_FastSelect(uint8 channel) CYREENTRANT;
void CapSense_CSD_AMuxCH0_DisconnectAll(void) CYREENTRANT;
/* The Connect and Disconnect functions are declared elsewhere */
/* void CapSense_CSD_AMuxCH0_Connect(uint8 channel); */
/* void CapSense_CSD_AMuxCH0_Disconnect(uint8 channel); */


/***************************************
*     Initial Parameter Constants
***************************************/

#define CapSense_CSD_AMuxCH0_CHANNELS  (2u + 2u +1u+ 0u)
#define CapSense_CSD_AMuxCH0_MUXTYPE   (1u)


/***************************************
*             API Constants
***************************************/

#define CapSense_CSD_AMuxCH0_NULL_CHANNEL   (0xFFu)
#define CapSense_CSD_AMuxCH0_MUX_SINGLE     (1u)
#define CapSense_CSD_AMuxCH0_MUX_DIFF       (2u)


/***************************************
*        Conditional Functions
***************************************/

#if (CapSense_CSD_AMuxCH0_MUXTYPE == CapSense_CSD_AMuxCH0_MUX_SINGLE)
#define CapSense_CSD_AMuxCH0_Connect(channel) CapSense_CSD_AMuxCH0_Set(channel)
#define CapSense_CSD_AMuxCH0_Disconnect(channel) CapSense_CSD_AMuxCH0_Unset(channel)
#else
    void CapSense_CSD_AMuxCH0_Connect(uint8 channel) CYREENTRANT;
    void CapSense_CSD_AMuxCH0_Disconnect(uint8 channel) CYREENTRANT;
#endif  /* End (CapSense_CSD_AMuxCH0_MUXTYPE == CapSense_CSD_AMuxCH0_MUX_SINGLE) */

#endif /* CY_CAPSENSE_CSD_AMUX_CapSense_CSD_AMuxCH0_H */


/* [] END OF FILE */
