Arnesh-sharma/P4P_Project-130/Testing Data/psoc_diode_test/psoc_code_base/CS301_Class.cydsn/main.c

/* ========================================
 * Fully working code: 
 * PWM      : 
 * Encoder  : 
 * ADC      :
 * USB      : port displays speed and position.
 * CMD: "PW xx"
 * Copyright Univ of Auckland, 2016
 * All Rights Reserved
 * UNPUBLISHED, LICENSED SOFTWARE.
 *
 * CONFIDENTIAL AND PROPRIETARY INFORMATION
 * WHICH IS THE PROPERTY OF Univ of Auckland.
 *
 * ========================================
*/
#include <stdio.h>
#include <string.h>
#include <stdlib.h>
#include <project.h>
//* ========================================
#include "defines.h"
#include "vars.h"
//* ========================================
void usbPutString(char *s);
void usbPutChar(char c);
void handle_usb();
//* ========================================

char buffer[64];
int16_t average = 0;
uint8_t idac_val = 100;

int main()
{
// --------------------------------    
// ----- INITIALIZATIONS ----------
    CYGlobalIntEnable;

// ------USB SETUP ----------------    
#ifdef USE_USB    
    USBUART_Start(0,USBUART_5V_OPERATION);
#endif        
        
    RF_BT_SELECT_Write(0);
    Opamp_1_Start();
    IDAC8_1_Start();
    //IDAC8_1_SetValue(idac_val);
    ADC_SAR_1_Start();
    ADC_SAR_1_StartConvert();
    for(;;)
    {
        /* Place your application code here. */
        //usbPutString(displaystring);
        handle_usb();
        if (flag_KB_string == 1)
        {
            usbPutString(line);
            flag_KB_string = 0;
        }      
        // IDAC Sweep
        for (int i = 0; i < 256; i++) {
            IDAC8_1_SetValue(i);
            // Get ADC value and transmit to screen
            int16_t result = 0;
            for (int j=0; j <= 10; j++) {
                 int16_t data = ADC_SAR_1_GetResult16(); 
                average += data;   
            }
            result = average/10;
            sprintf(buffer, "IDAC Val: %u, Pin Val: %d \r\n", i, result);
            usbPutString(buffer);
            average = 0;
        }
        CyDelay(5000);
    }   
}
//* ========================================
void usbPutString(char *s)
{
// !! Assumes that *s is a string with allocated space >=64 chars     
//  Since USB implementation retricts data packets to 64 chars, this function truncates the
//  length to 62 char (63rd char is a '!')

#ifdef USE_USB     
    while (USBUART_CDCIsReady() == 0);
    s[63]='\0';
    s[62]='!';
    USBUART_PutData((uint8*)s,strlen(s));
#endif
}
//* ========================================
void usbPutChar(char c)
{
#ifdef USE_USB     
    while (USBUART_CDCIsReady() == 0);
    USBUART_PutChar(c);
#endif    
}
//* ========================================
void handle_usb()
{
    // handles input at terminal, echos it back to the terminal
    // turn echo OFF, key emulation: only CR
    // entered string is made available in 'line' and 'flag_KB_string' is set
    
    static uint8 usbStarted = FALSE;
    static uint16 usbBufCount = 0;
    uint8 c; 
    

    if (!usbStarted)
    {
        if (USBUART_GetConfiguration())
        {
            USBUART_CDC_Init();
            usbStarted = TRUE;
        }
    }
    else
    {
        if (USBUART_DataIsReady() != 0)
        {  
            c = USBUART_GetChar();

            if ((c == 13) || (c == 10))
            {
//                if (usbBufCount > 0)
                {
                    entry[usbBufCount]= '\0';
                    strcpy(line,entry);
                    usbBufCount = 0;
                    flag_KB_string = 1;
                }
            }
            else 
            {
                if (((c == CHAR_BACKSP) || (c == CHAR_DEL) ) && (usbBufCount > 0) )
                    usbBufCount--;
                else
                {
                    if (usbBufCount > (BUF_SIZE-2) ) // one less else strtok triggers a crash
                    {
                       USBUART_PutChar('!');        
                    }
                    else
                        entry[usbBufCount++] = c;  
                }  
            }
        }
    }    
}


/* [] END OF FILE */
