Arnesh-sharma/P4P_Project-130/Testing Data/psoc_diode_test/psoc_code_base/CS301_Class.cydsn/codegentemp/diode_pin_aliases.h

/*******************************************************************************
* File Name: diode_pin.h  
* Version 2.20
*
* Description:
*  This file contains the Alias definitions for Per-Pin APIs in cypins.h. 
*  Information on using these APIs can be found in the System Reference Guide.
*
* Note:
*
********************************************************************************
* Copyright 2008-2015, Cypress Semiconductor Corporation.  All rights reserved.
* You may use this file only in accordance with the license, terms, conditions, 
* disclaimers, and limitations in the end user license agreement accompanying 
* the software package with which this file was provided.
*******************************************************************************/

#if !defined(CY_PINS_diode_pin_ALIASES_H) /* Pins diode_pin_ALIASES_H */
#define CY_PINS_diode_pin_ALIASES_H

#include "cytypes.h"
#include "cyfitter.h"


/***************************************
*              Constants        
***************************************/
#define diode_pin_0			(diode_pin__0__PC)
#define diode_pin_0_INTR	((uint16)((uint16)0x0001u << diode_pin__0__SHIFT))

#define diode_pin_INTR_ALL	 ((uint16)(diode_pin_0_INTR))

#endif /* End Pins diode_pin_ALIASES_H */


/* [] END OF FILE */
