Arnesh-sharma/P4P_Project-130/Photos/photos of sensors/IMG_6684.JPG

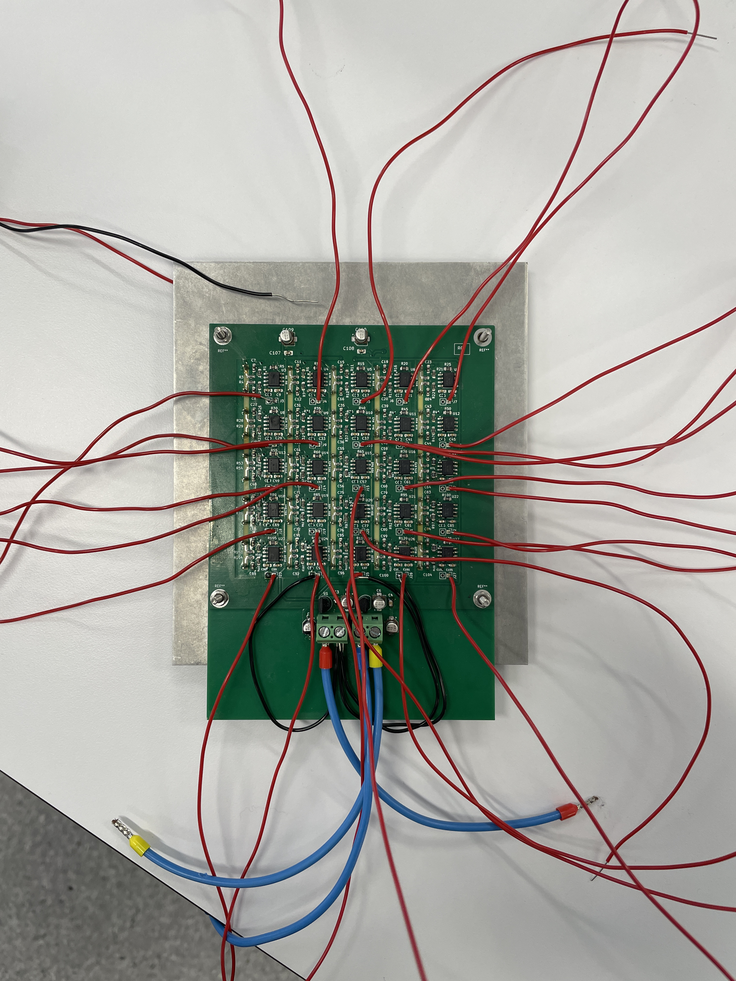
Photos/photos of sensors/IMG_6684.JPG
